Majklzbastlirny/WeatherStation/Code/Frontend/NodeRED/NodeRed-Flow.png

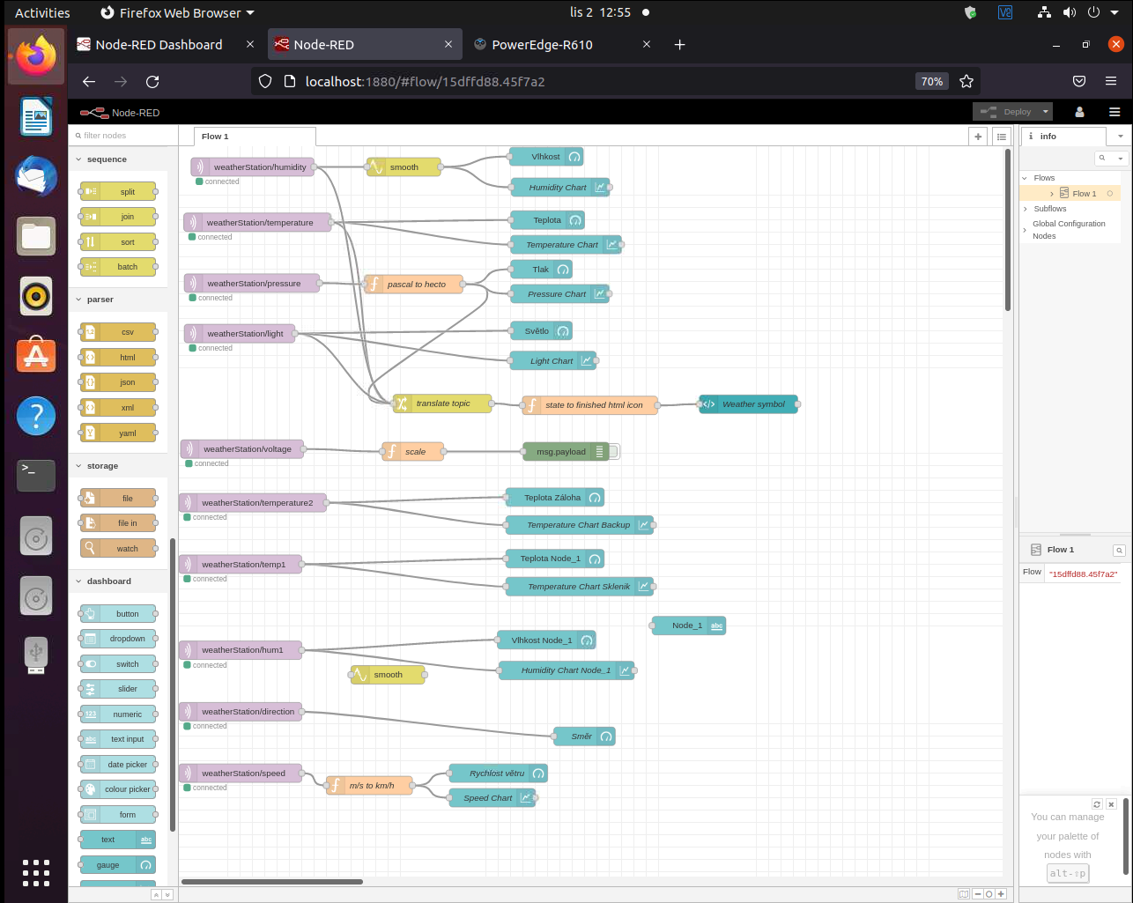
Code/Frontend/NodeRED/NodeRed-Flow.png
