Majklzbastlirny/WeatherStation/Code/Frontend/NodeRED/NodeRed-GUI.png

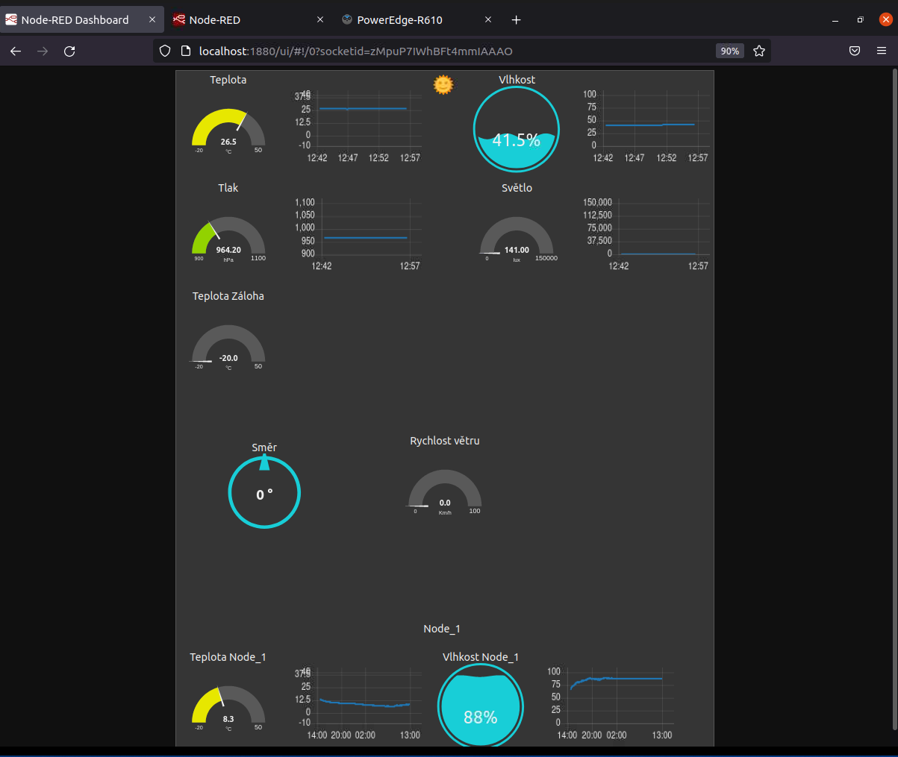
Code/Frontend/NodeRED/NodeRed-GUI.png
