Majklzbastlirny/WeatherStation/Documentation/1646741958582.jpg

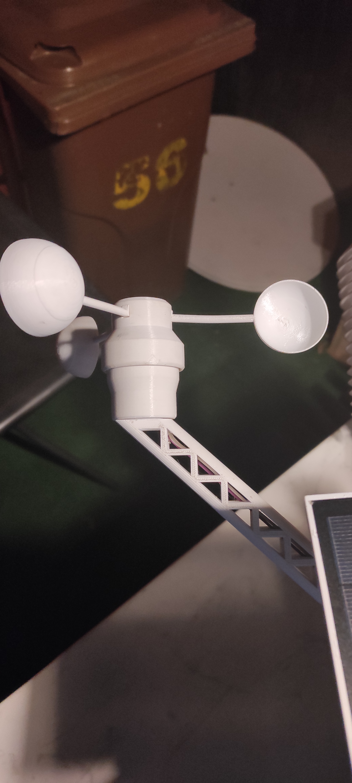
Documentation/1646741958582.jpg
