Majklzbastlirny/WeatherStation/Documentation/akumulátor.webp

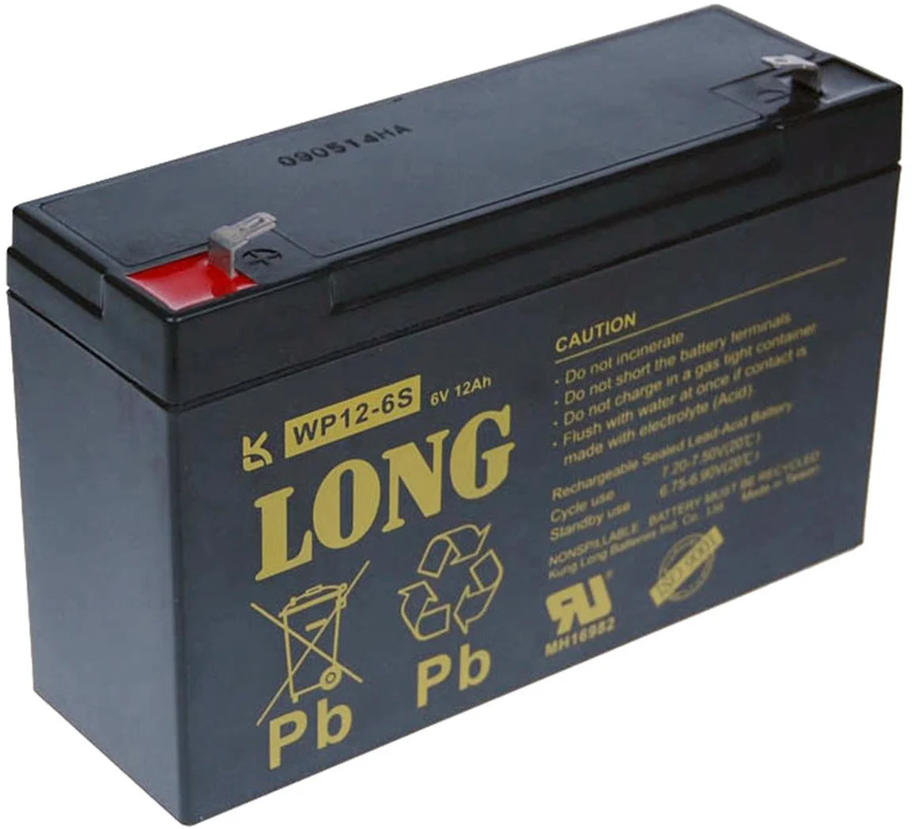
Documentation/akumulátor.webp
