Majklzbastlirny/WeatherStation/Documentation/Anemometr.jpg

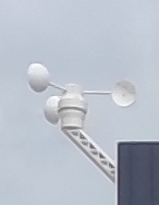
Documentation/Anemometr.jpg
