Majklzbastlirny/WeatherStation/Documentation/Anemometr_Base.png

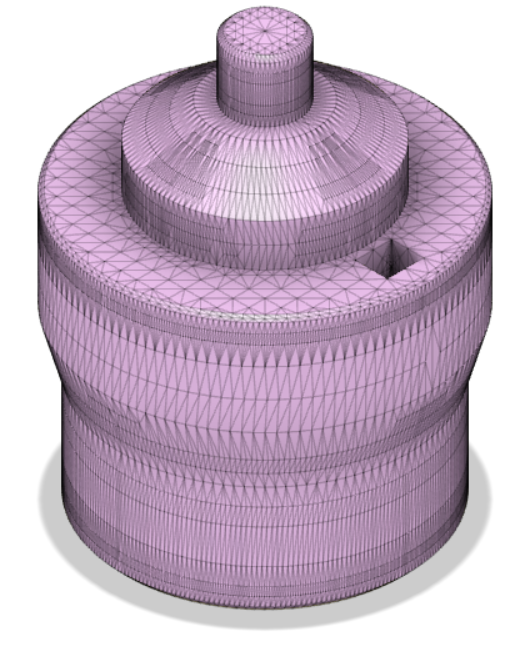
Documentation/Anemometr_Base.png
