Majklzbastlirny/WeatherStation/Documentation/Anemometr_Kryt.png

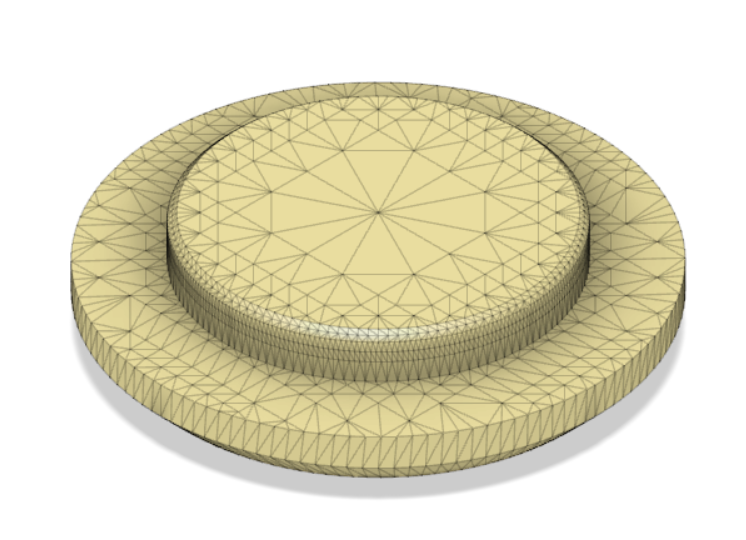
Documentation/Anemometr_Kryt.png
