Majklzbastlirny/WeatherStation/Documentation/Anemometr_Lopatka.png

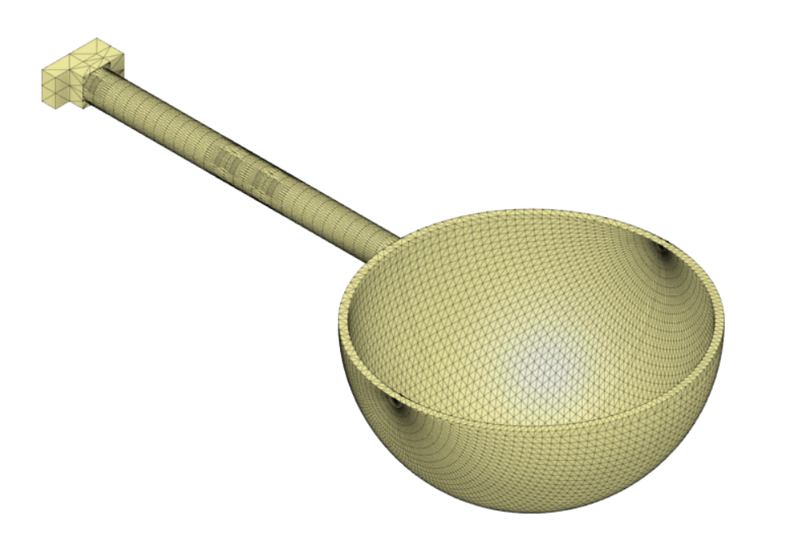
Documentation/Anemometr_Lopatka.png
