Majklzbastlirny/WeatherStation/Documentation/Anemometr_Tělo.png

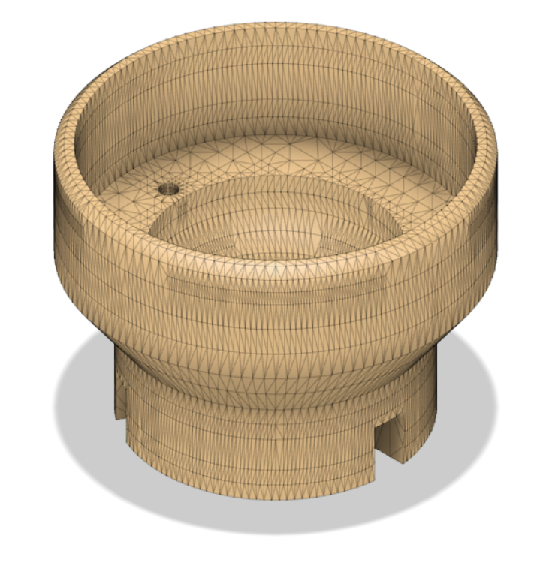
Documentation/Anemometr_Tělo.png
