Majklzbastlirny/WeatherStation/Documentation/BH1750.jpg

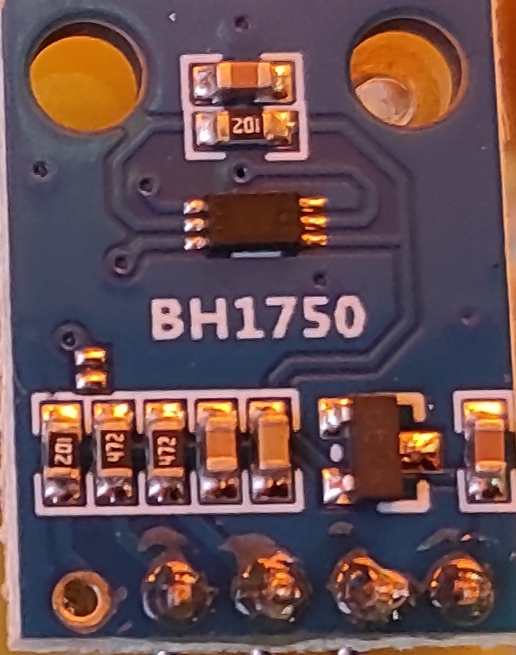
Documentation/BH1750.jpg
