Majklzbastlirny/WeatherStation/Documentation/blokove eink.png

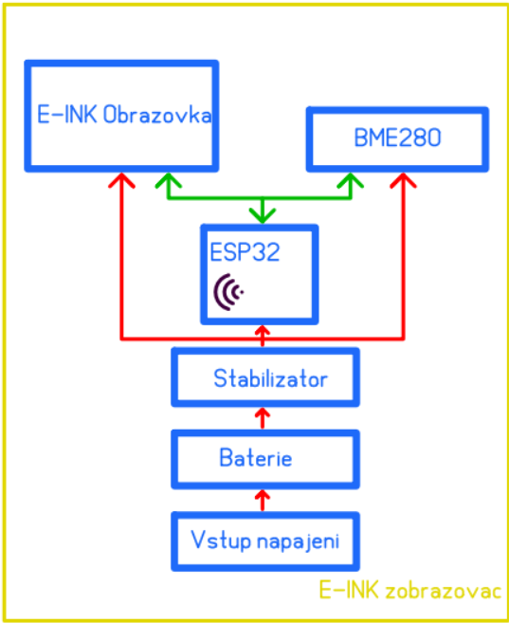
Documentation/blokove eink.png
