Majklzbastlirny/WeatherStation/Documentation/blokove meteo.png

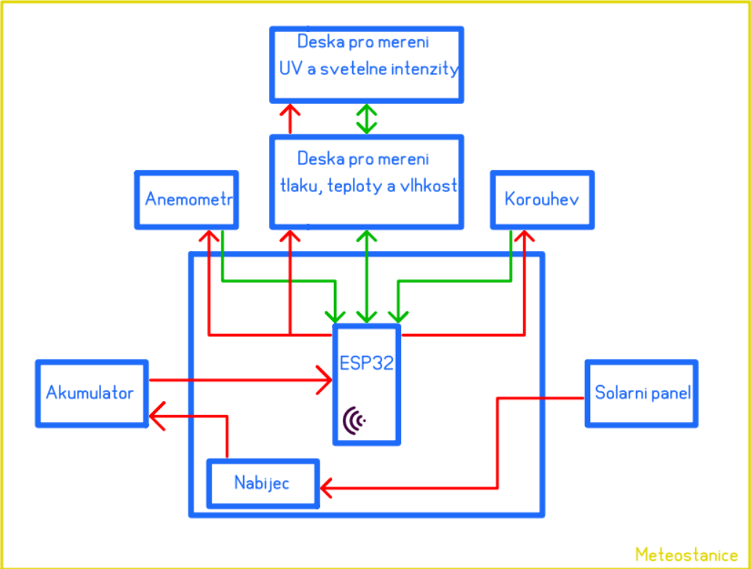
Documentation/blokove meteo.png
