Majklzbastlirny/WeatherStation/Documentation/Blokove oled.png

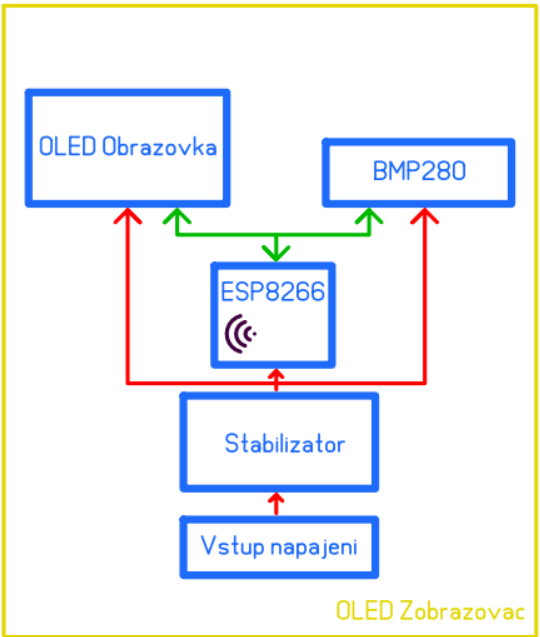
Documentation/Blokove oled.png
