Majklzbastlirny/WeatherStation/Documentation/BMP280.jpg

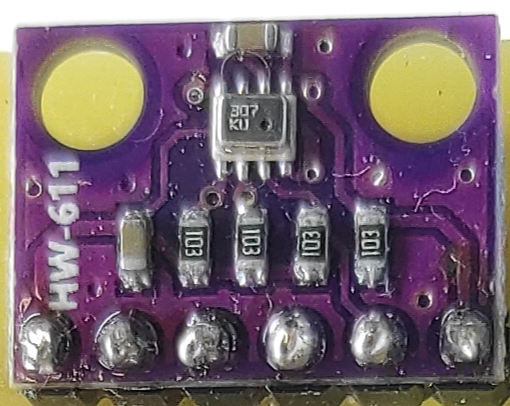
Documentation/BMP280.jpg
