Majklzbastlirny/WeatherStation/Documentation/Deska senzorů 1 - PCB/Deska senzorů 1 - PCB-1.png

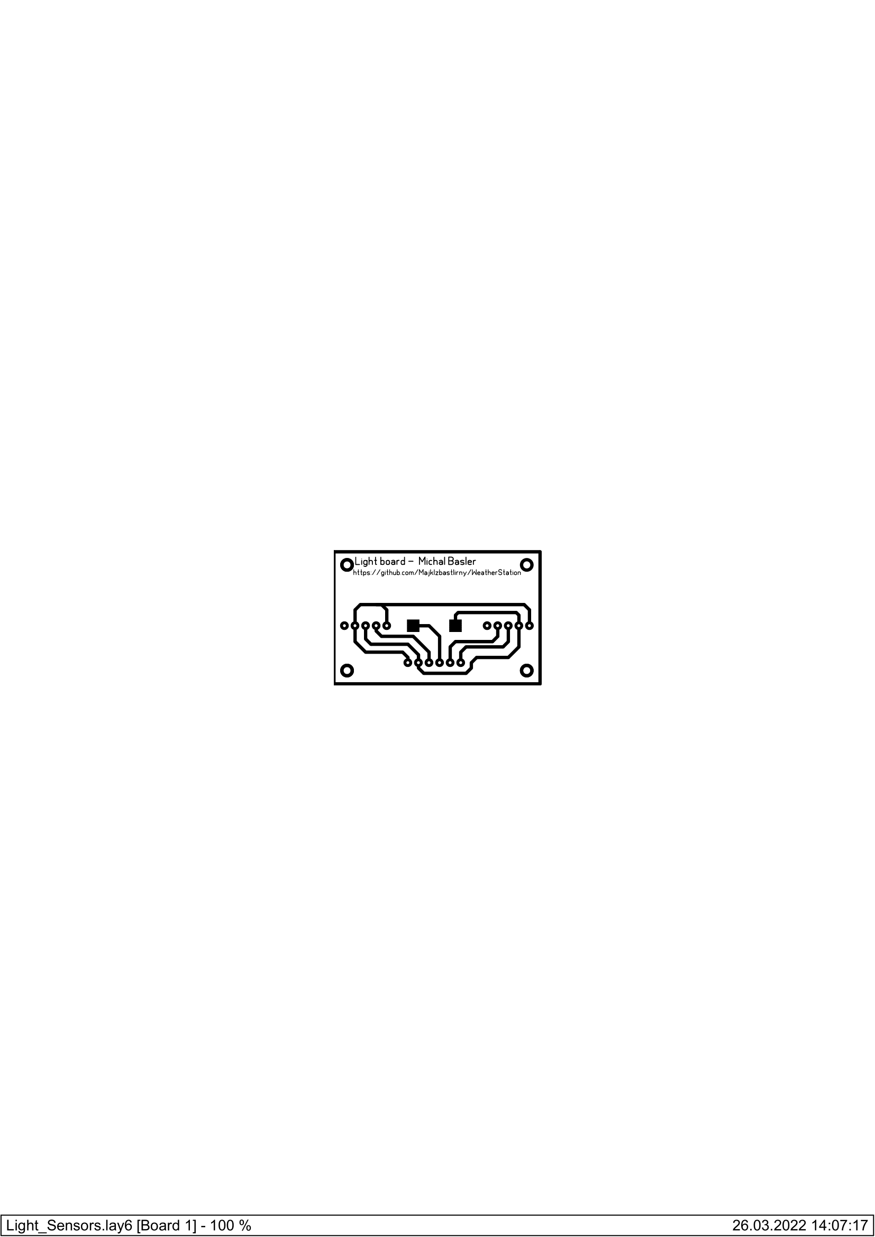
Documentation/Deska senzorů 1 - PCB/Deska senzorů 1 - PCB-1.png
