Majklzbastlirny/WeatherStation/Documentation/Deska senzorů 1/Deska senzorů 1-1.png

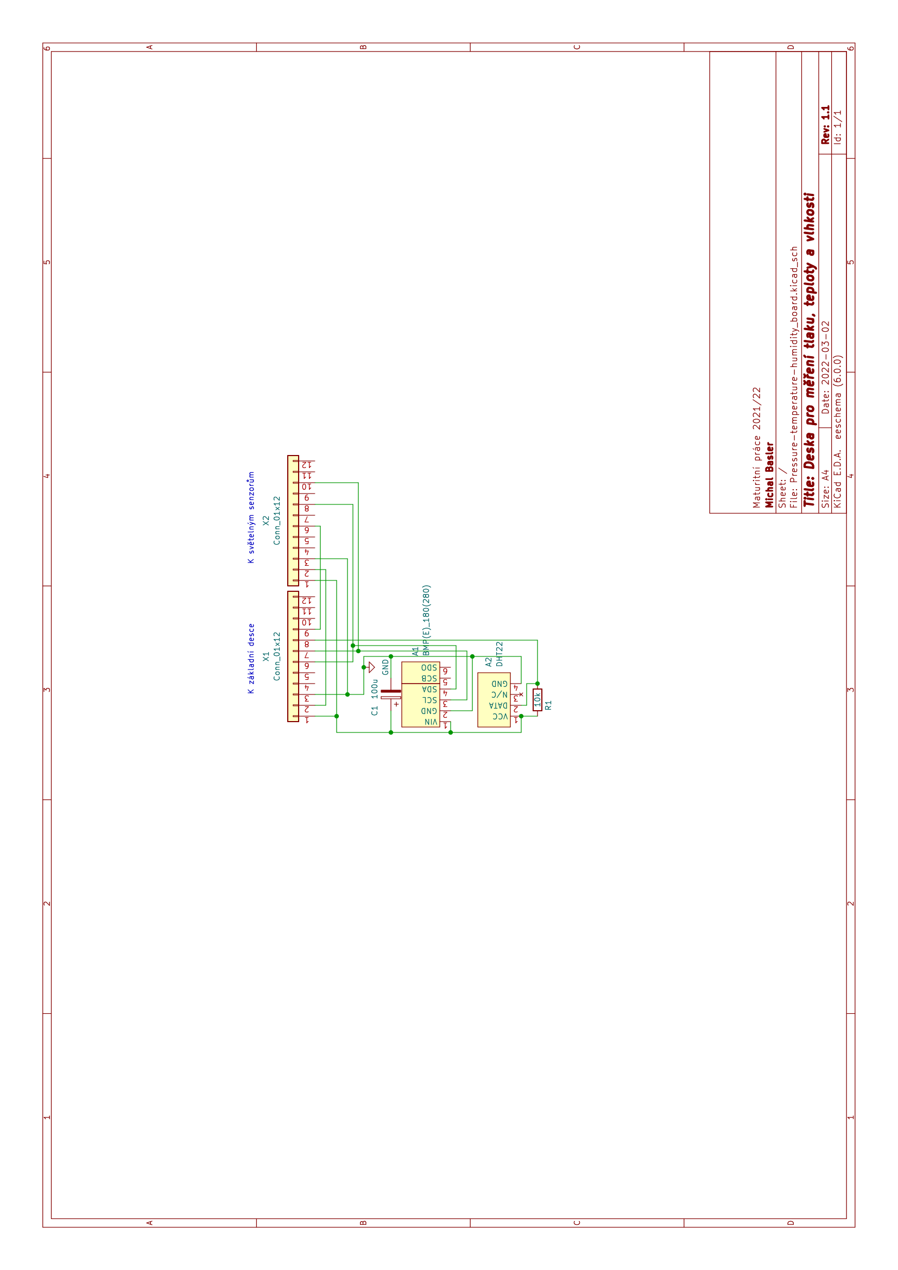
Documentation/Deska senzorů 1/Deska senzorů 1-1.png
