Majklzbastlirny/WeatherStation/Documentation/DHT22.jpg

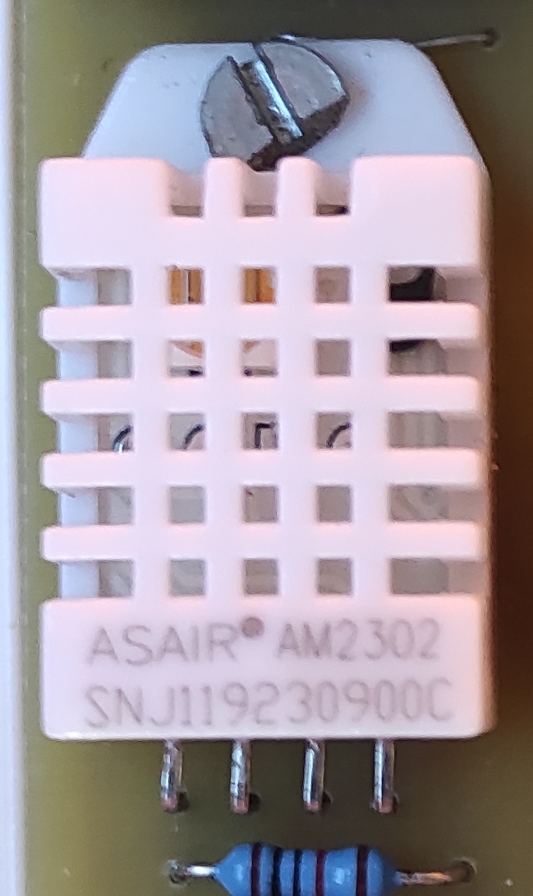
Documentation/DHT22.jpg
