Majklzbastlirny/WeatherStation/Documentation/Držák_Anemometr.png

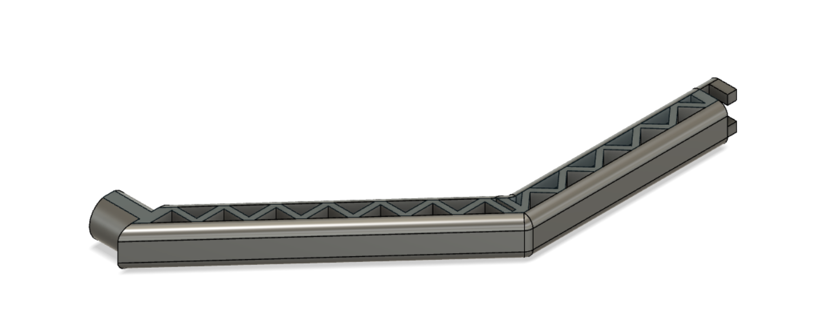
Documentation/Držák_Anemometr.png
