Majklzbastlirny/WeatherStation/Documentation/Držák_Korouhev.png

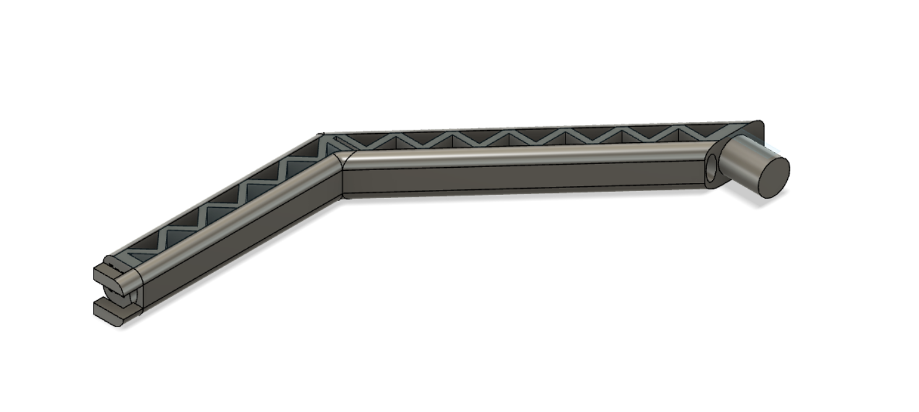
Documentation/Držák_Korouhev.png
