Majklzbastlirny/WeatherStation/Documentation/Držák_Senzory.png

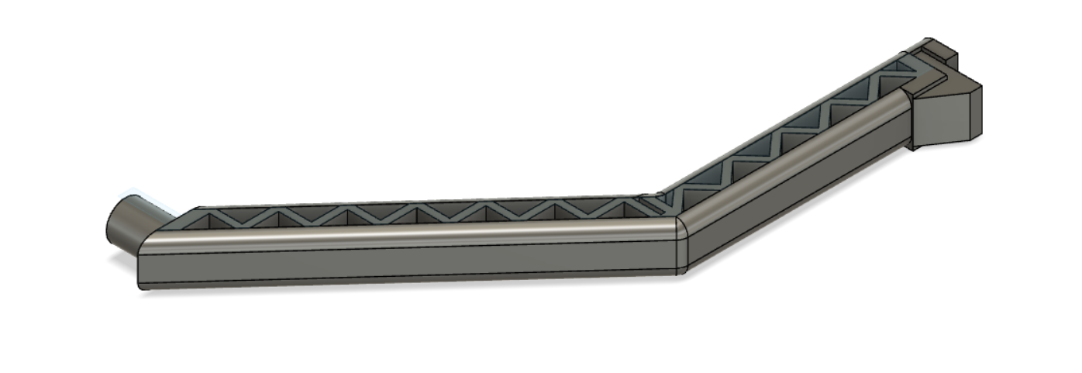
Documentation/Držák_Senzory.png
