Majklzbastlirny/WeatherStation/Documentation/Držák_Vše.png

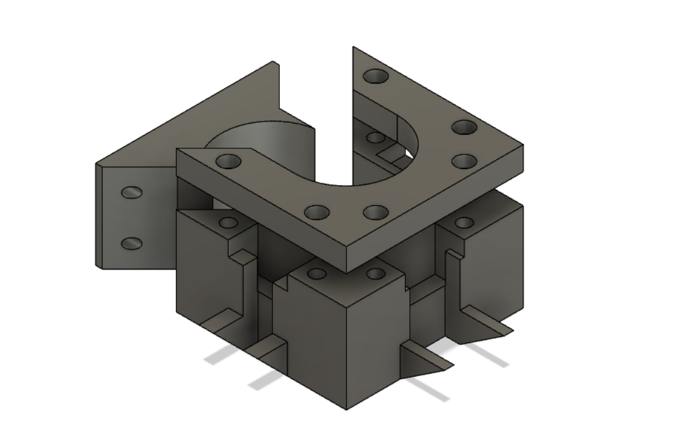
Documentation/Držák_Vše.png
