Majklzbastlirny/WeatherStation/Documentation/ESP_32.jpg

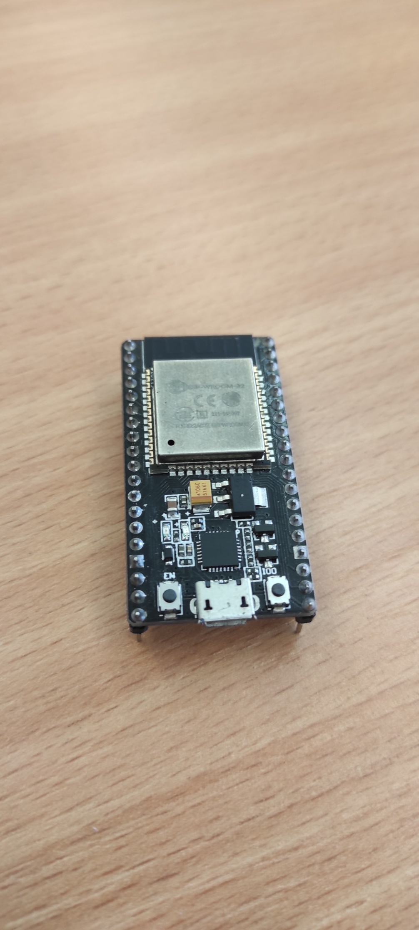
Documentation/ESP_32.jpg
