Majklzbastlirny/WeatherStation/Documentation/Home_Unit-OLED_Traces.BMP

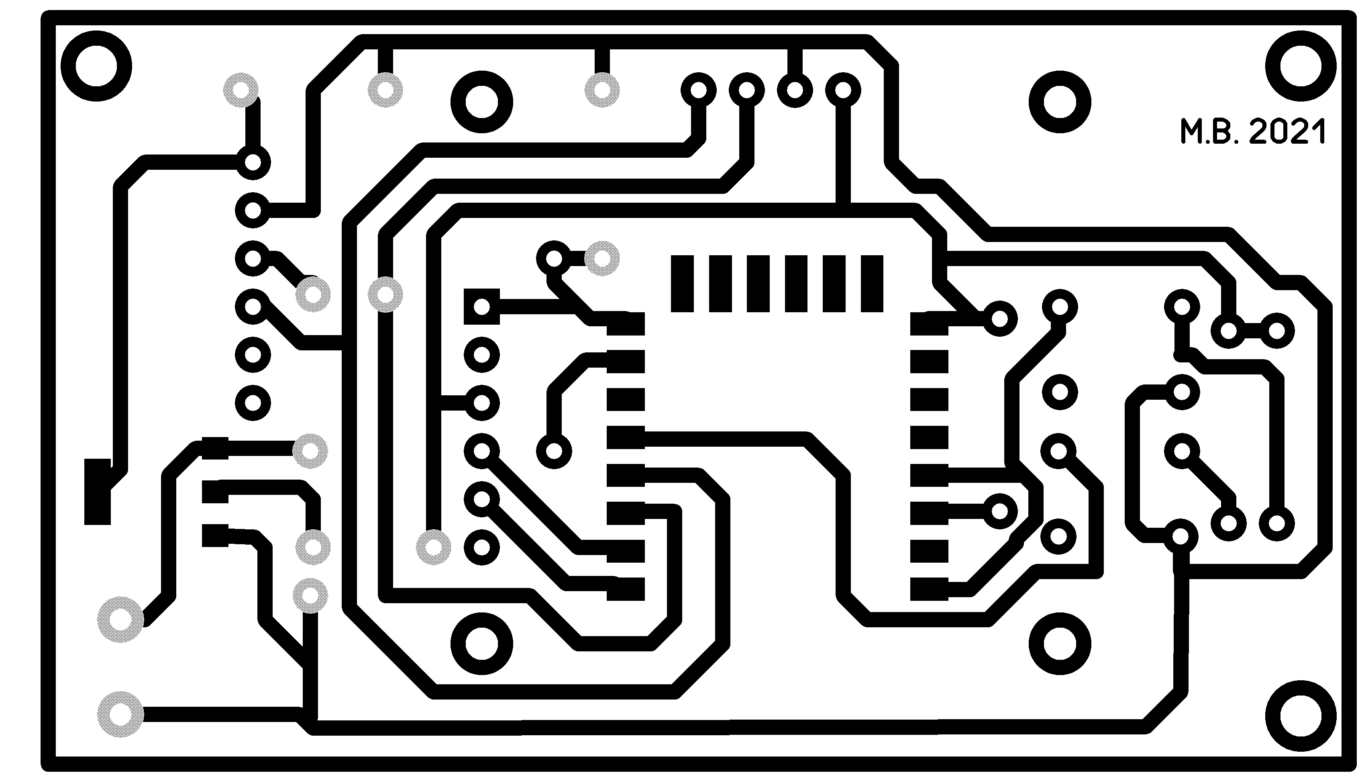
Documentation/Home_Unit-OLED_Traces.BMP
