Majklzbastlirny/WeatherStation/Documentation/IMG_20211102_125426.jpg

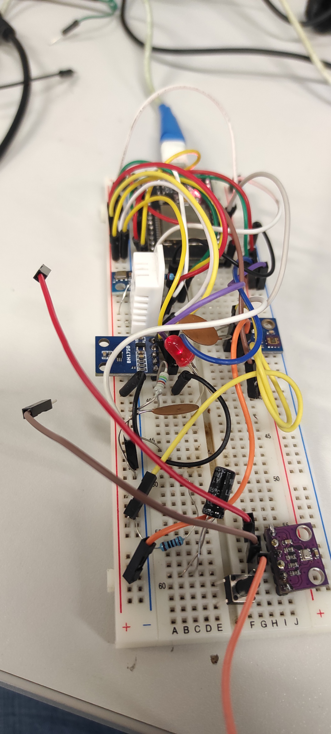
Documentation/IMG_20211102_125426.jpg
