Majklzbastlirny/WeatherStation/Documentation/IMG_20220214_152526.jpg

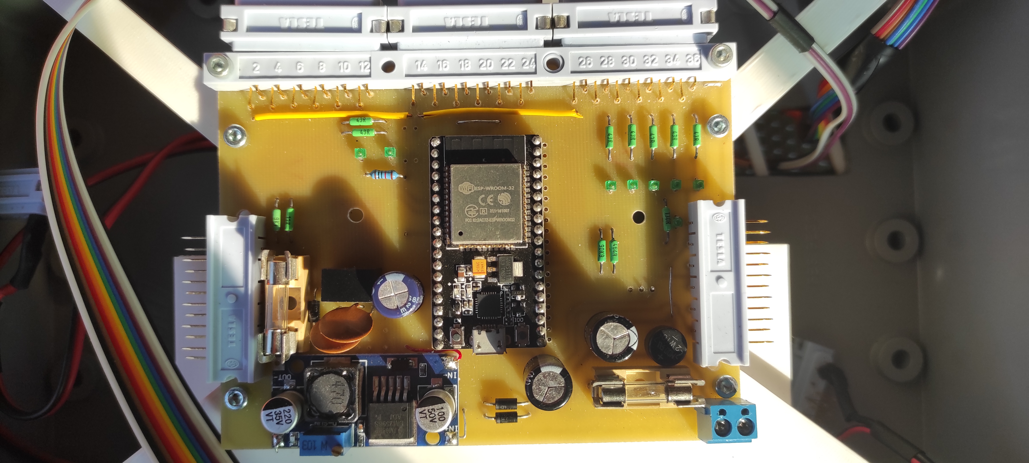
Documentation/IMG_20220214_152526.jpg
