Majklzbastlirny/WeatherStation/Documentation/IMG_20220214_152532.jpg

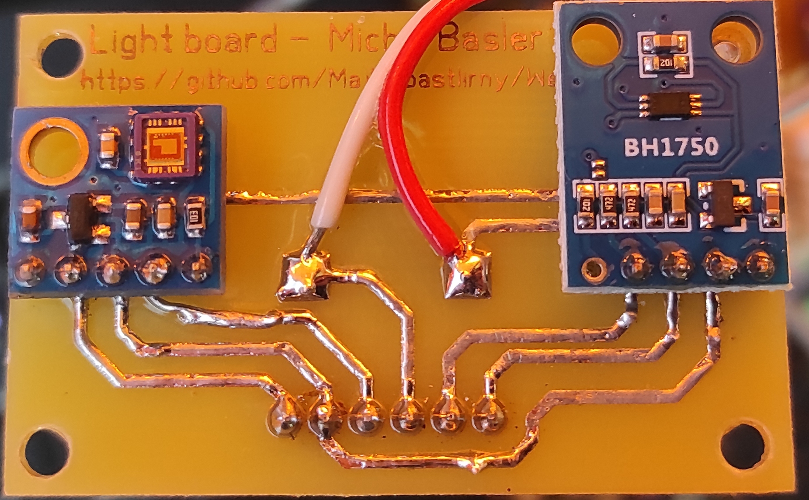
Documentation/IMG_20220214_152532.jpg
