Majklzbastlirny/WeatherStation/Documentation/IMG_20220214_152558.jpg

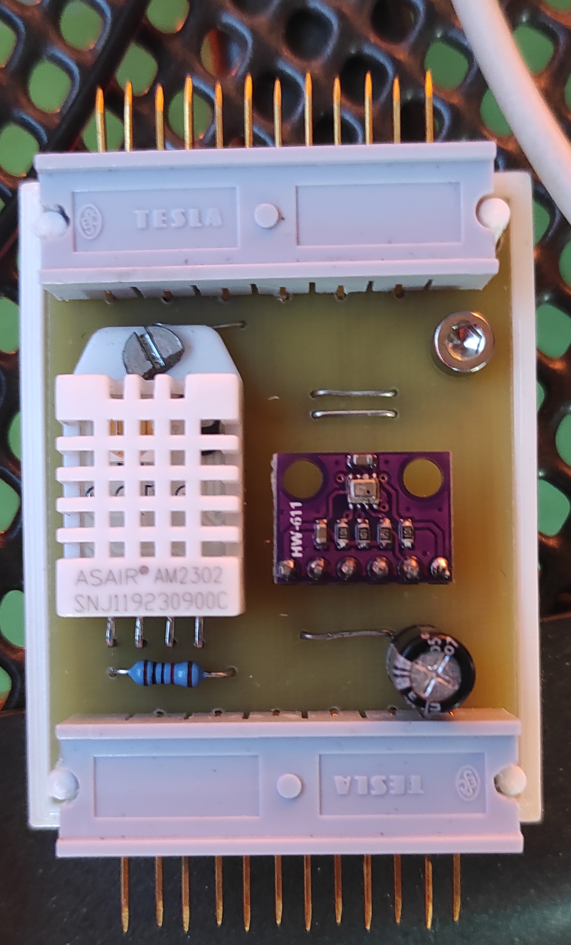
Documentation/IMG_20220214_152558.jpg
