Majklzbastlirny/WeatherStation/Documentation/IMG_20220214_160920.jpg

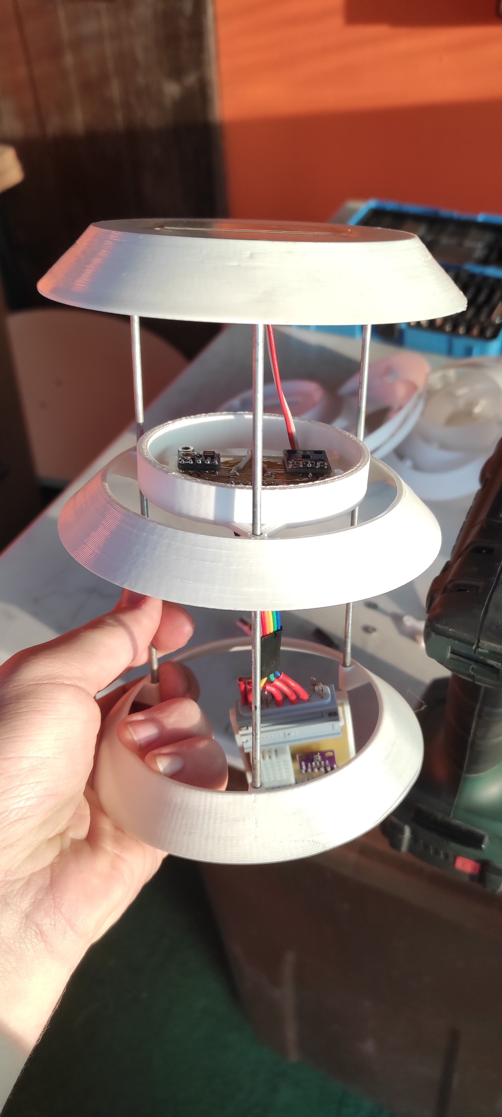
Documentation/IMG_20220214_160920.jpg
