Majklzbastlirny/WeatherStation/Documentation/IMG_20220302_161140.jpg

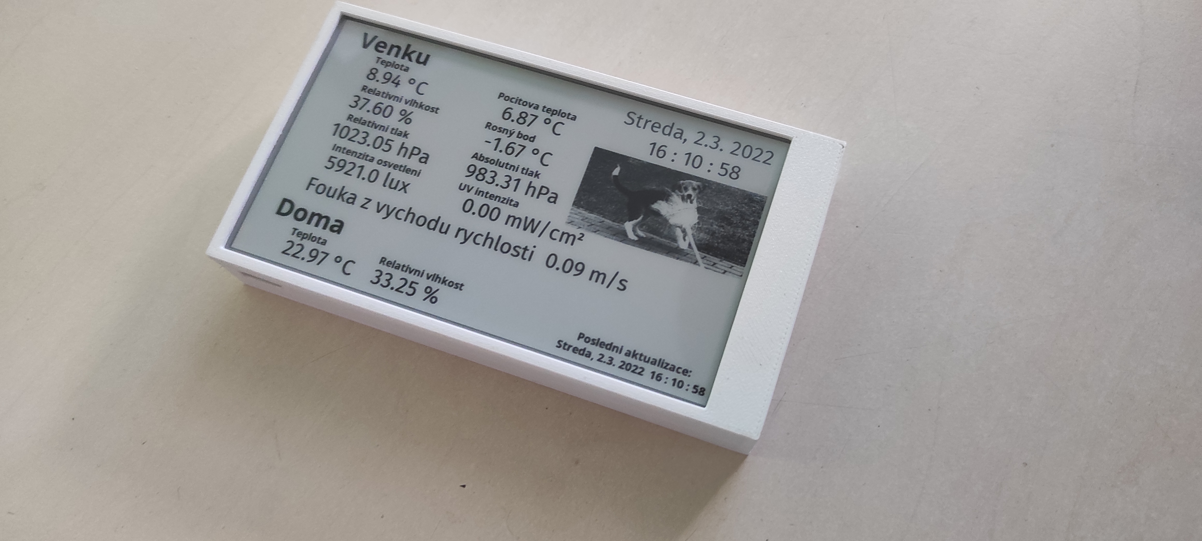
Documentation/IMG_20220302_161140.jpg
