Majklzbastlirny/WeatherStation/Documentation/IMG_20220302_161202.jpg

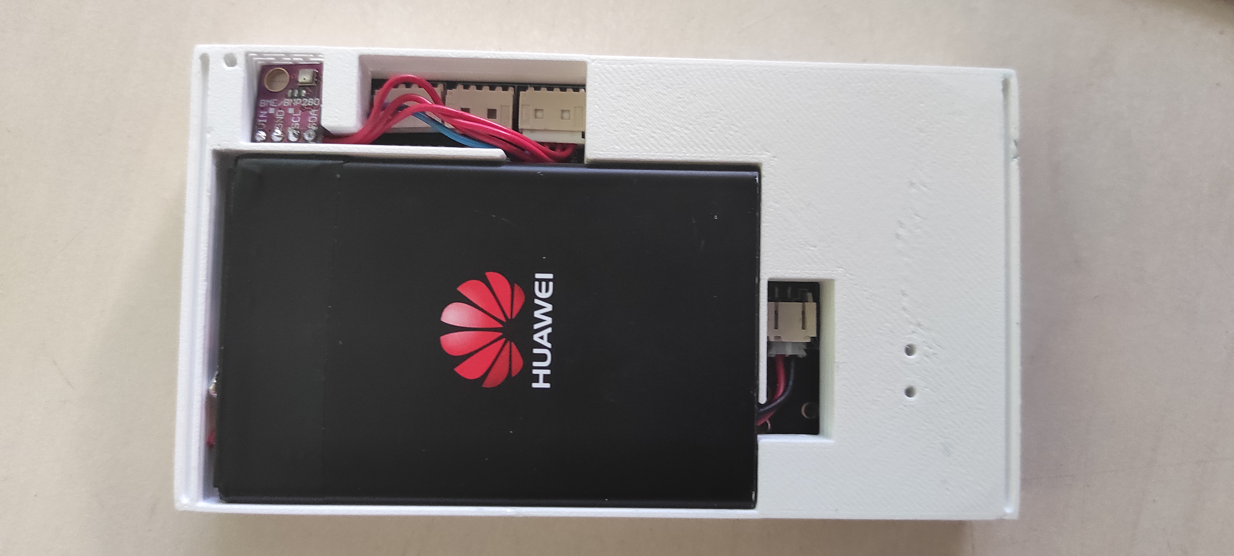
Documentation/IMG_20220302_161202.jpg
