Majklzbastlirny/WeatherStation/Documentation/IMG_20220303_124802.jpg

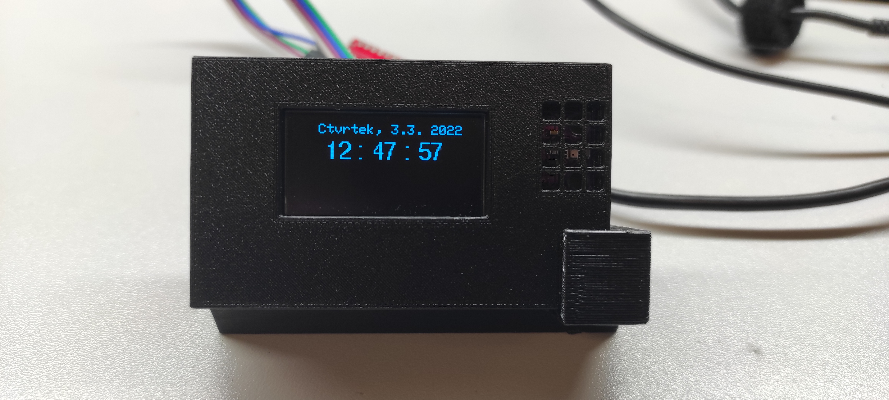
Documentation/IMG_20220303_124802.jpg
