Majklzbastlirny/WeatherStation/Documentation/IMG_20220303_124805.jpg

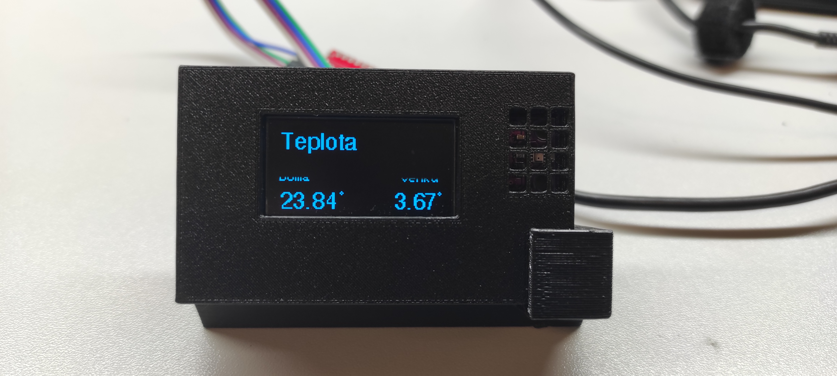
Documentation/IMG_20220303_124805.jpg
