Majklzbastlirny/WeatherStation/Documentation/IMG_20220303_124854.jpg

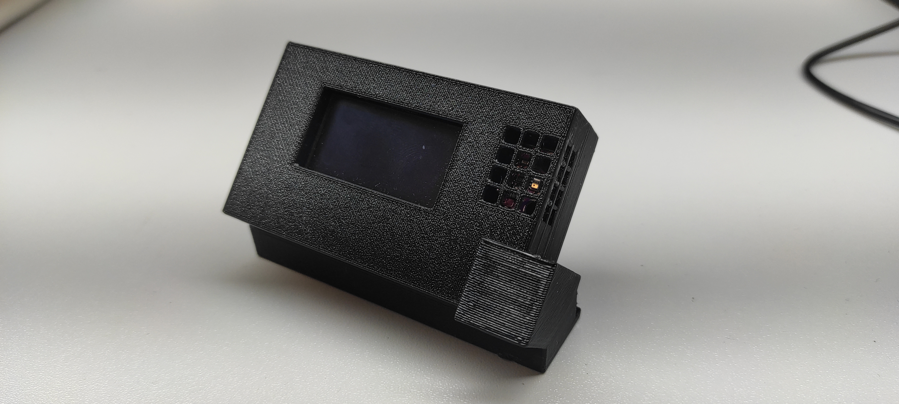
Documentation/IMG_20220303_124854.jpg
