Majklzbastlirny/WeatherStation/Documentation/IMG_20220303_124949.jpg

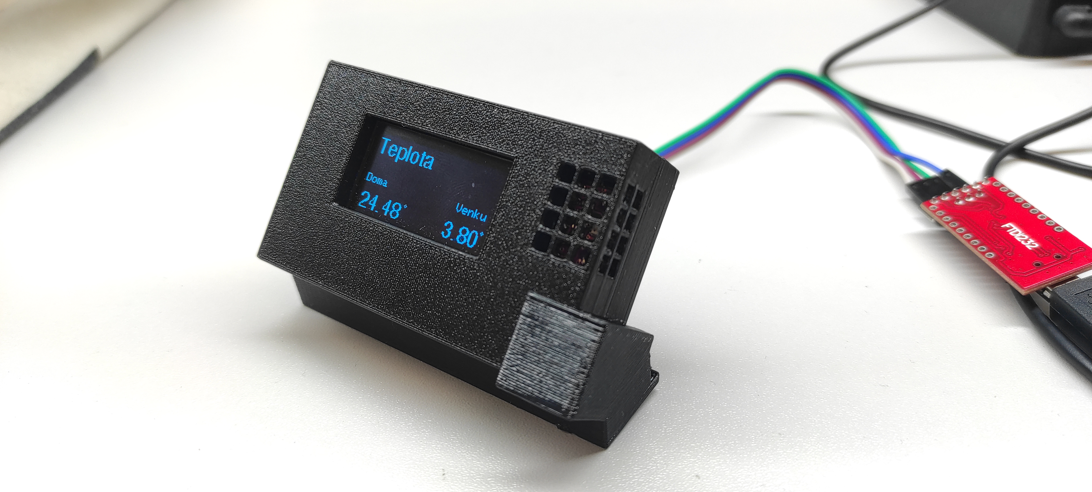
Documentation/IMG_20220303_124949.jpg
