Majklzbastlirny/WeatherStation/Documentation/IMG_20220303_125136_1.jpg

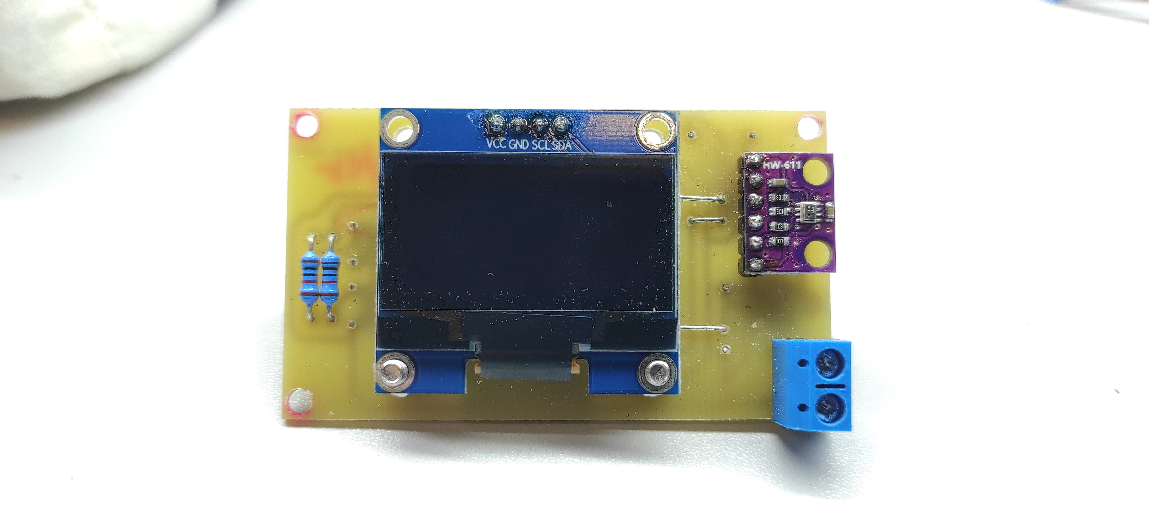
Documentation/IMG_20220303_125136_1.jpg
