Majklzbastlirny/WeatherStation/Documentation/IMG_20220303_125144.jpg

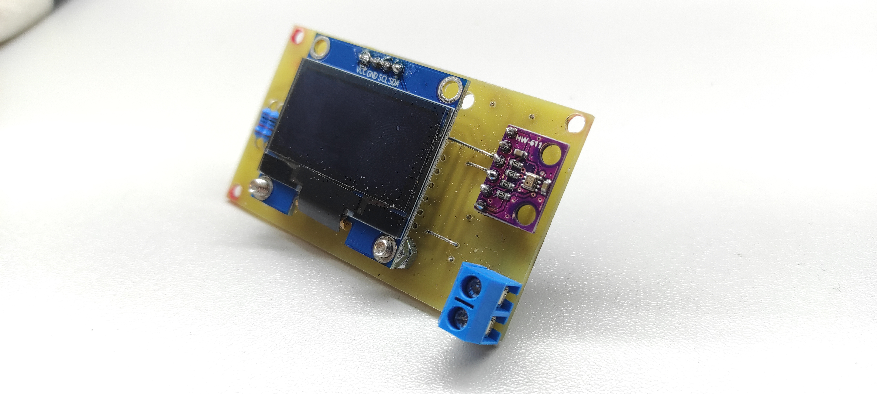
Documentation/IMG_20220303_125144.jpg
