Majklzbastlirny/WeatherStation/Documentation/Korouhev.jpg

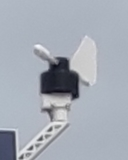
Documentation/Korouhev.jpg
