Majklzbastlirny/WeatherStation/Documentation/LED_Indikátory.jpg

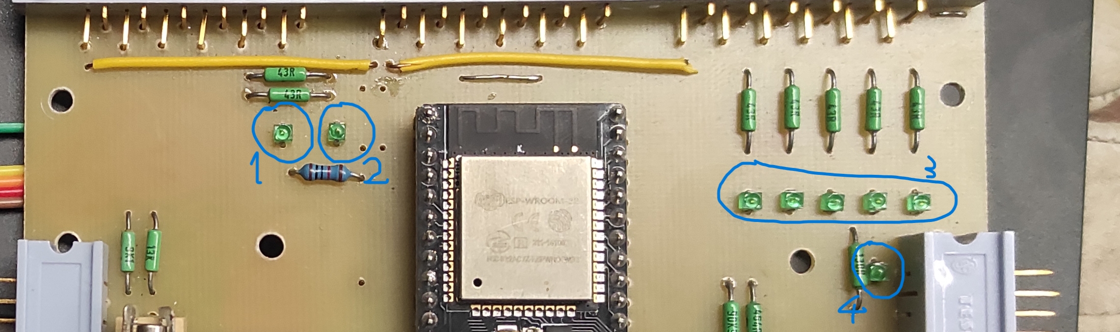
Documentation/LED_Indikátory.jpg
