Majklzbastlirny/WeatherStation/Documentation/Light_Board_Traces.BMP

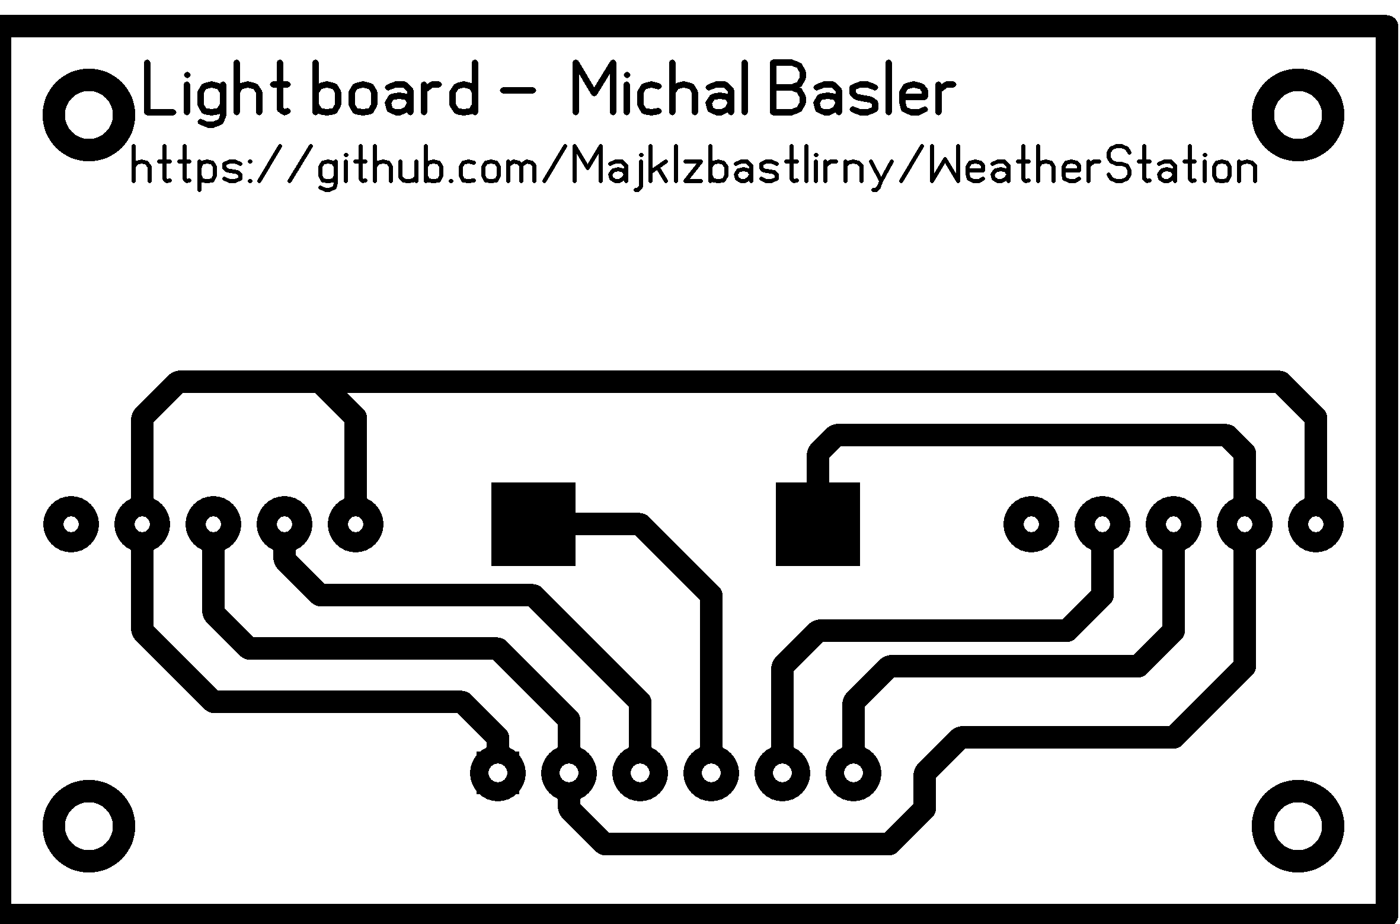
Documentation/Light_Board_Traces.BMP
