Majklzbastlirny/WeatherStation/Documentation/Main board - PCB/Main board - PCB-1.png

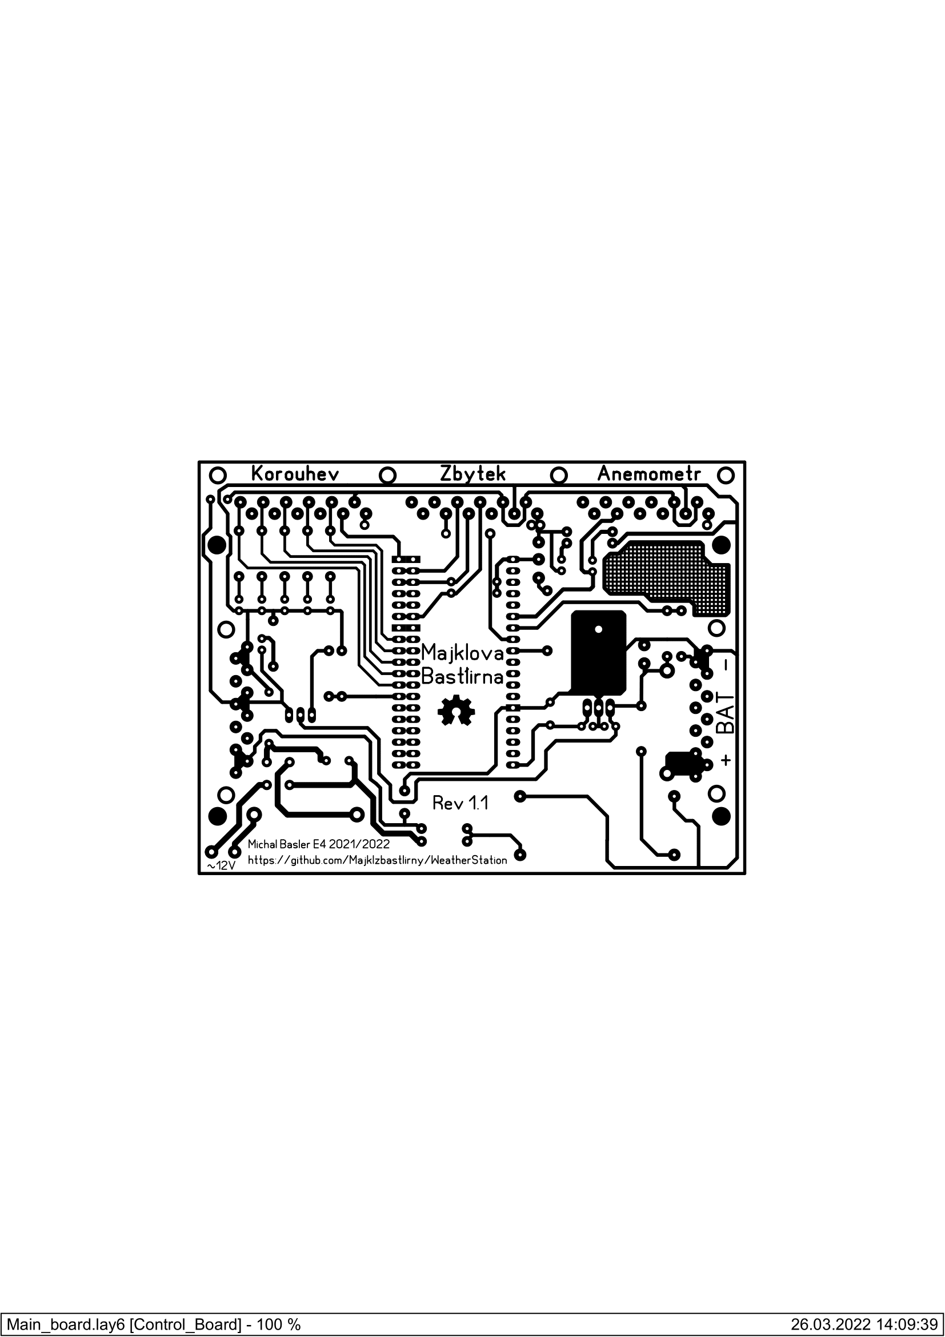
Documentation/Main board - PCB/Main board - PCB-1.png
