Majklzbastlirny/WeatherStation/Documentation/ML8511.jpg

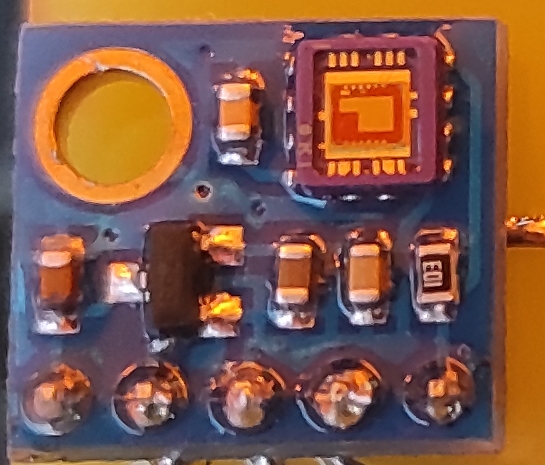
Documentation/ML8511.jpg
