Majklzbastlirny/WeatherStation/Documentation/Mounts.png

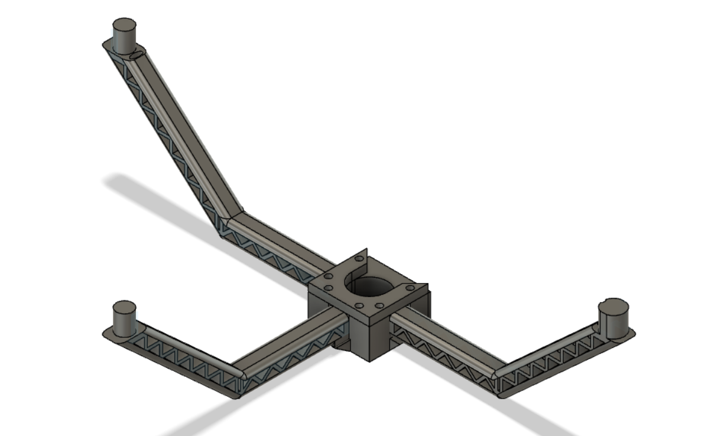
Documentation/Mounts.png
