Majklzbastlirny/WeatherStation/Documentation/OLED_Zobrazovač/OLED_Zobrazovač-1.png

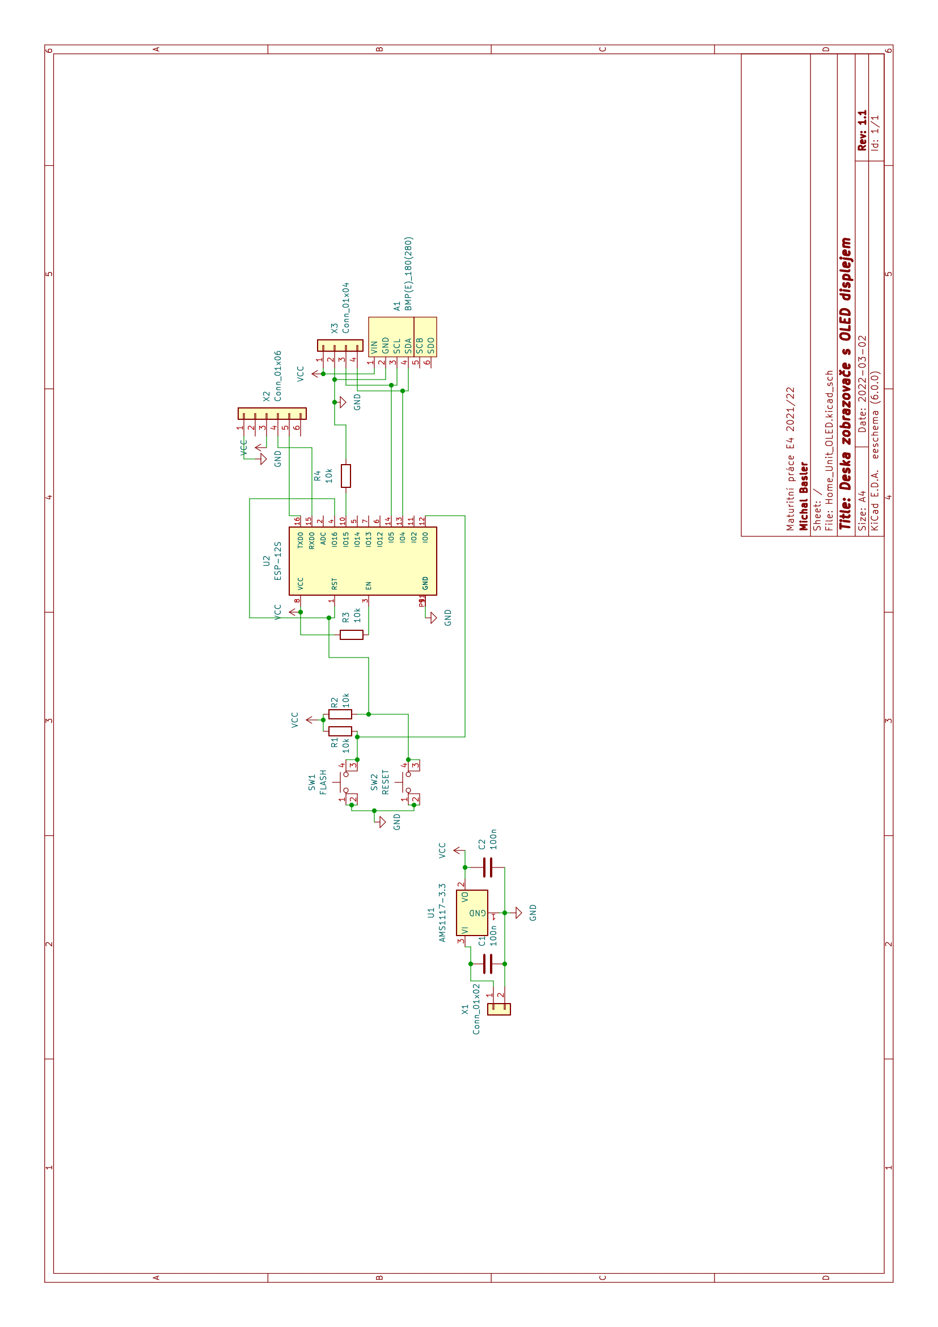
Documentation/OLED_Zobrazovač/OLED_Zobrazovač-1.png
