Majklzbastlirny/WeatherStation/Documentation/Osazovák_základnídeska.png

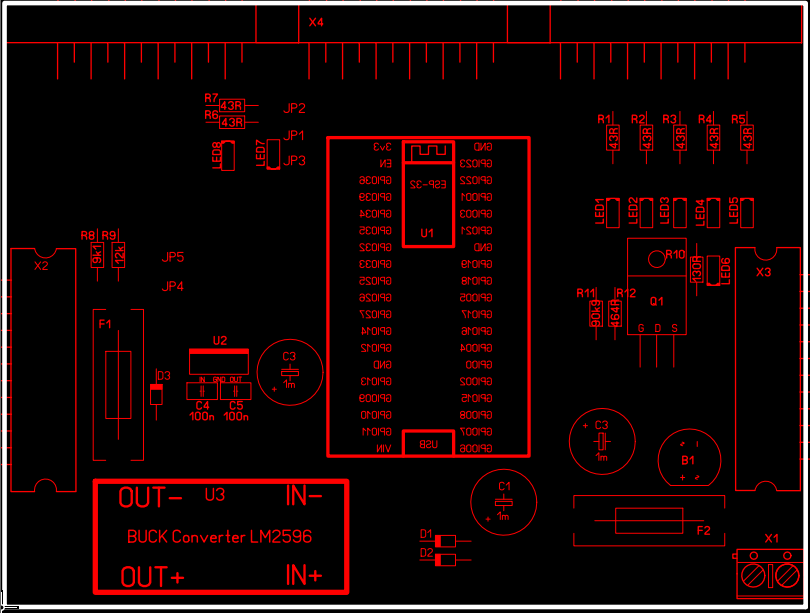
Documentation/Osazovák_základnídeska.png
