Majklzbastlirny/WeatherStation/Documentation/Screenshot_2022-04-21-14-04-22-356_com.mightyit.mqttclientterminal.jpg

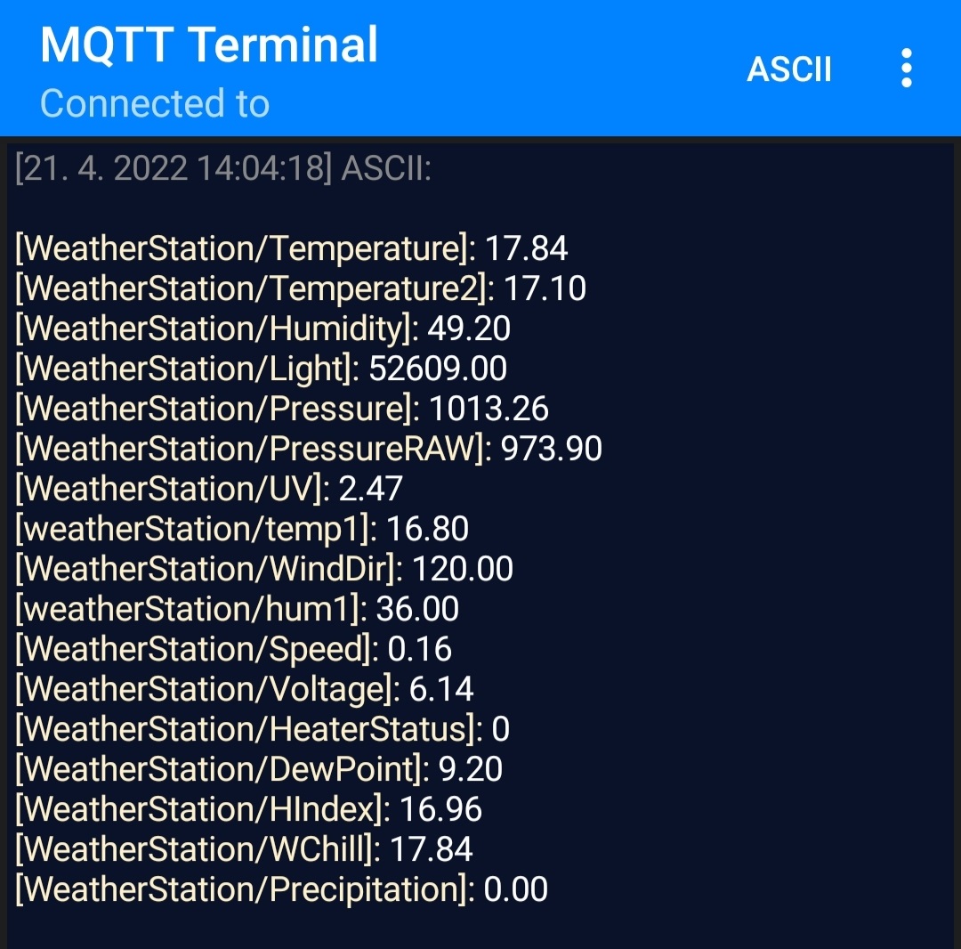
Documentation/Screenshot_2022-04-21-14-04-22-356_com.mightyit.mqttclientterminal.jpg
