Majklzbastlirny/WeatherStation/Documentation/Spínač-PCB/Spínač-PCB-1.png

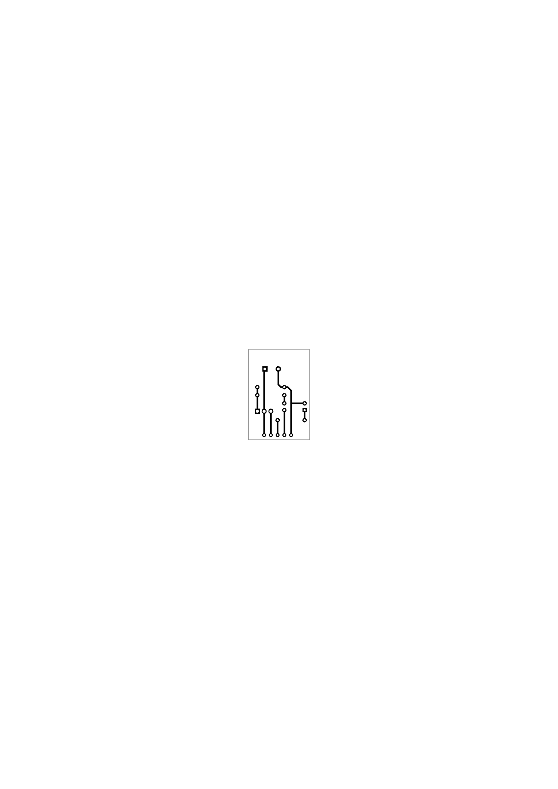
Documentation/Spínač-PCB/Spínač-PCB-1.png
