Majklzbastlirny/WeatherStation/Documentation/Switching_Obvody.jpg

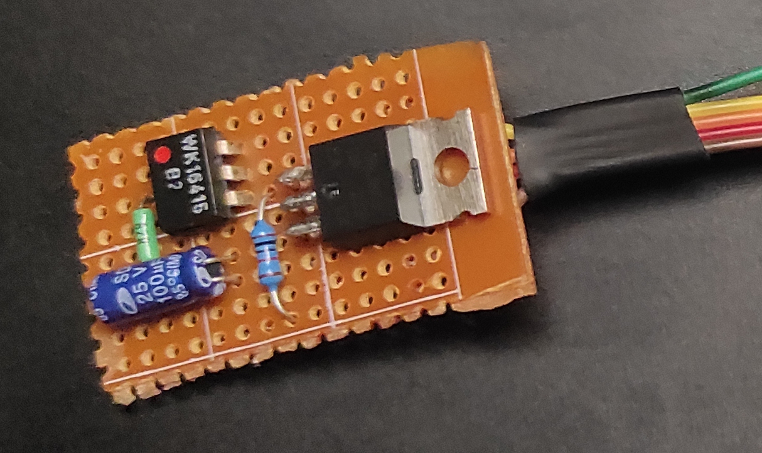
Documentation/Switching_Obvody.jpg
