Majklzbastlirny/WeatherStation/Documentation/Výsledek EINK.jpg

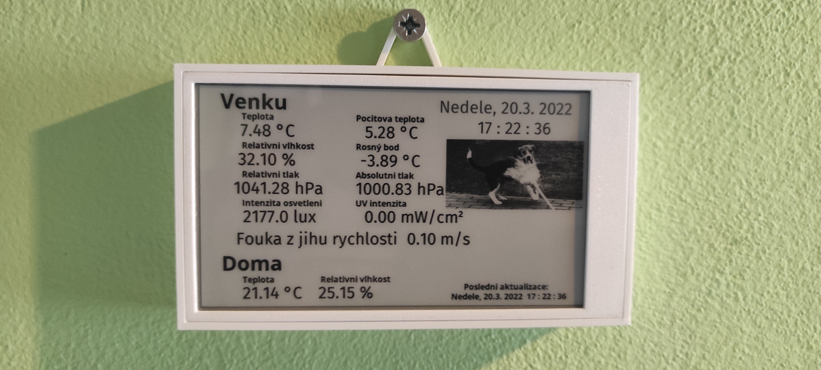
Documentation/Výsledek EINK.jpg
