Majklzbastlirny/WeatherStation/Documentation/Výsledek MQTT.jpg

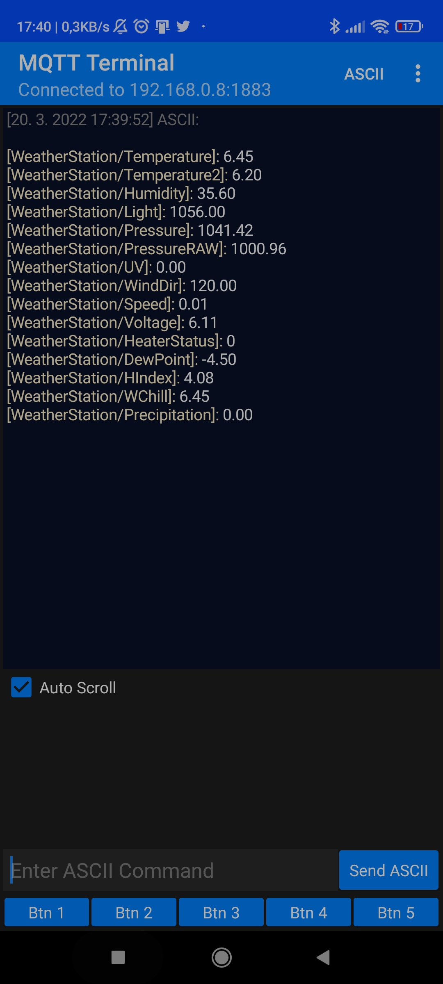
Documentation/Výsledek MQTT.jpg
