Majklzbastlirny/WeatherStation/Documentation/Výsledek OLED.jpg

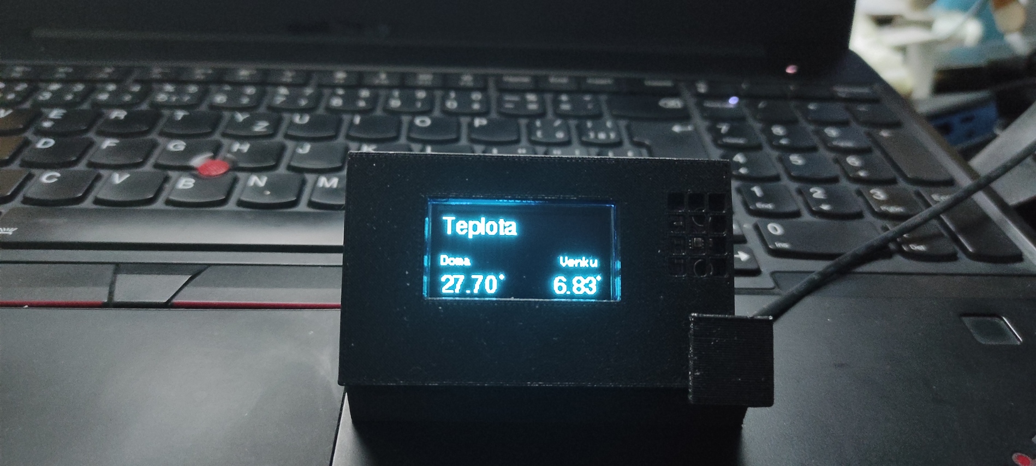
Documentation/Výsledek OLED.jpg
