Majklzbastlirny/WeatherStation/Documentation/Základka/Základní deska.png

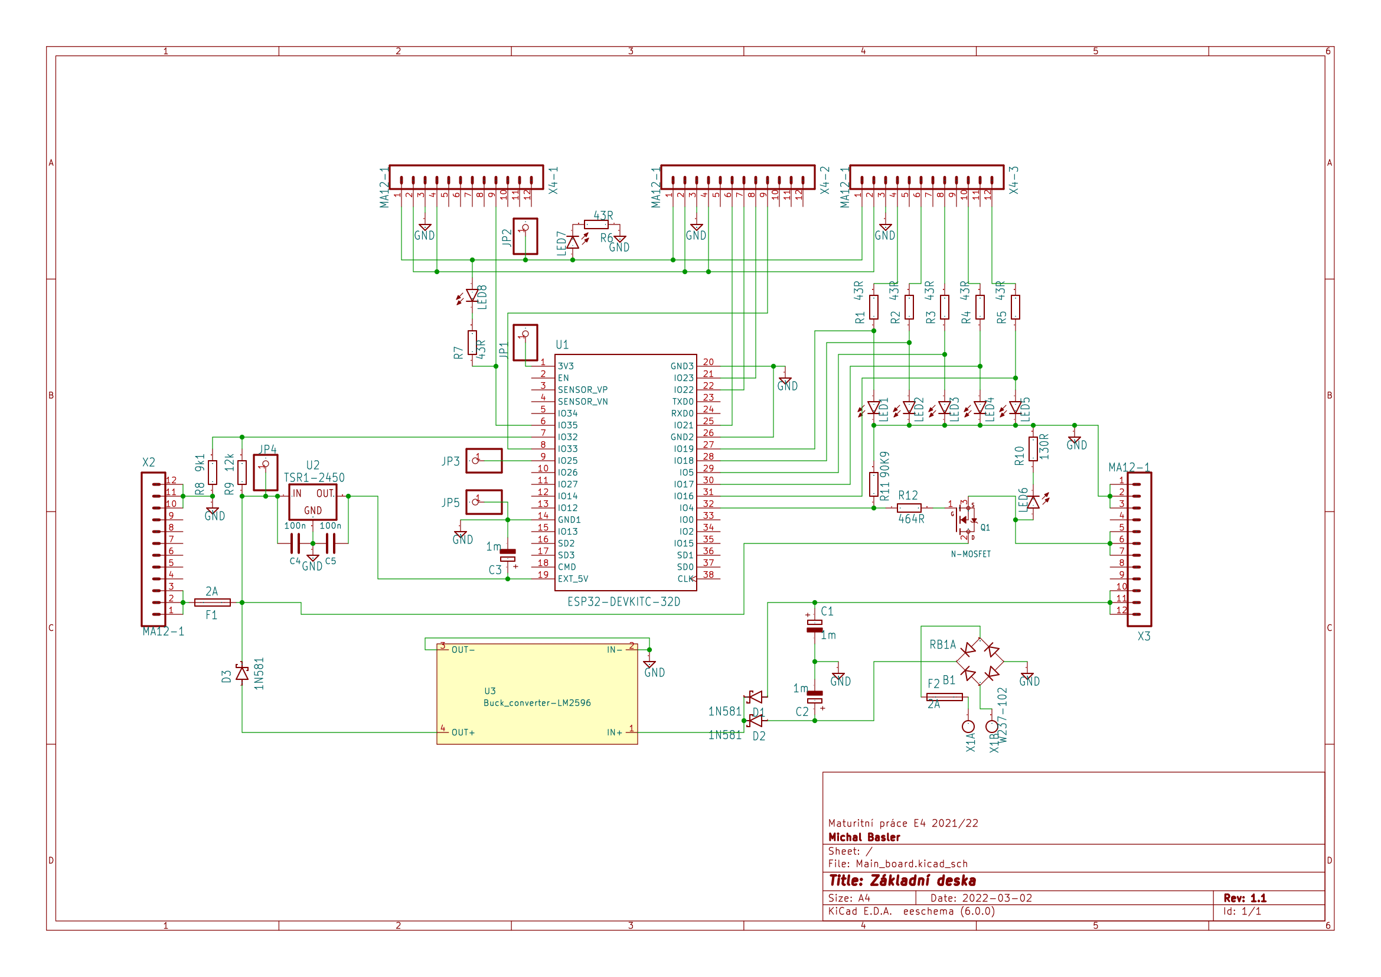
Documentation/Základka/Základní deska.png
