Majklzbastlirny/WeatherStation/Documentation/Štít-Držák.png

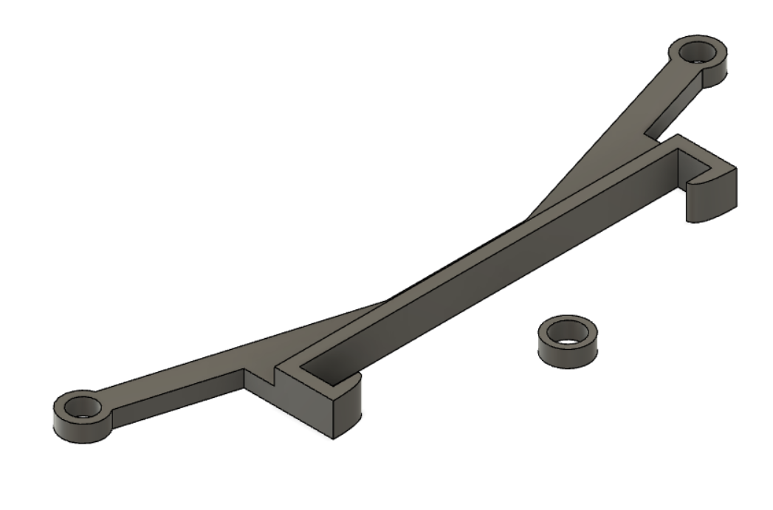
Documentation/Štít-Držák.png
