Majklzbastlirny/WeatherStation/Documentation/Štít-Kryt.png

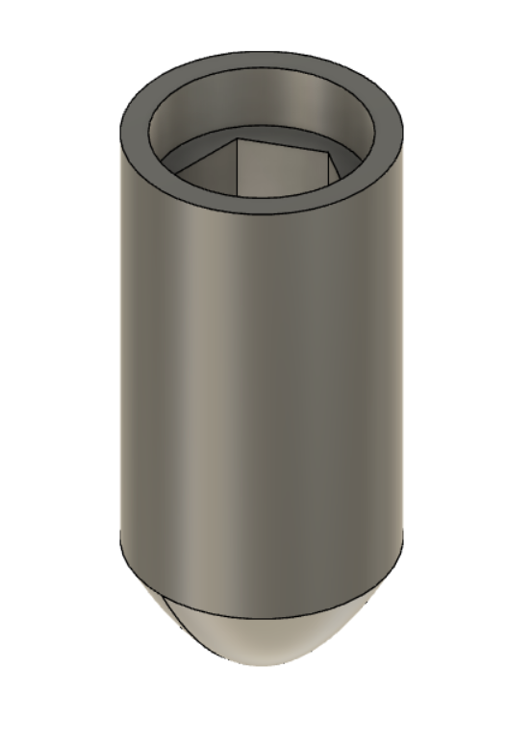
Documentation/Štít-Kryt.png
