Majklzbastlirny/WeatherStation/Documentation/Štít-Senzory.png

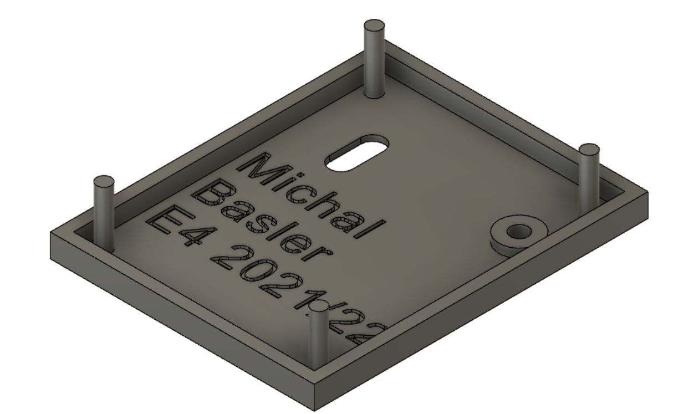
Documentation/Štít-Senzory.png
