Majklzbastlirny/WeatherStation/Documentation/Štít-Spodek.png

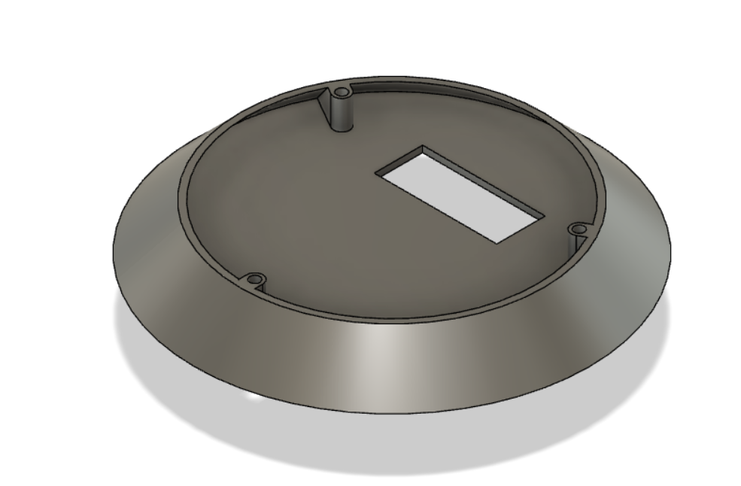
Documentation/Štít-Spodek.png
