Majklzbastlirny/WeatherStation/Documentation/Štít-Střed.png

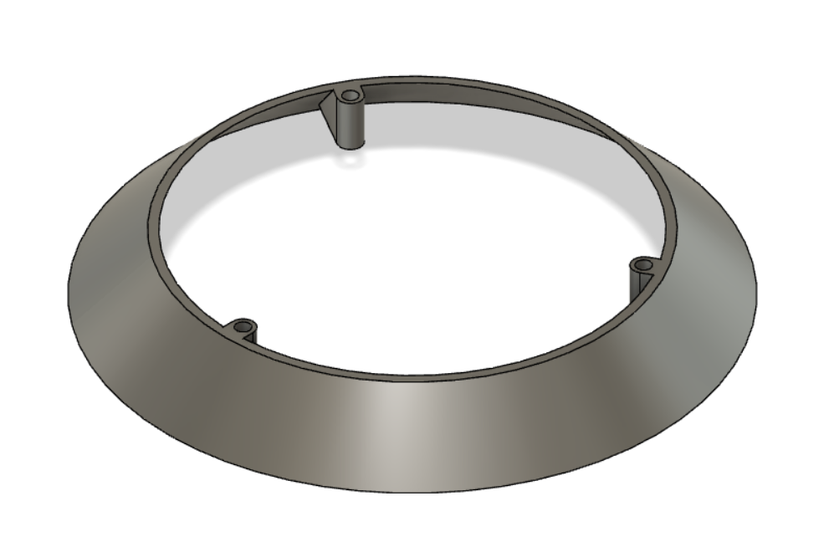
Documentation/Štít-Střed.png
