Majklzbastlirny/WeatherStation/Documentation/Štít-Světlo.png

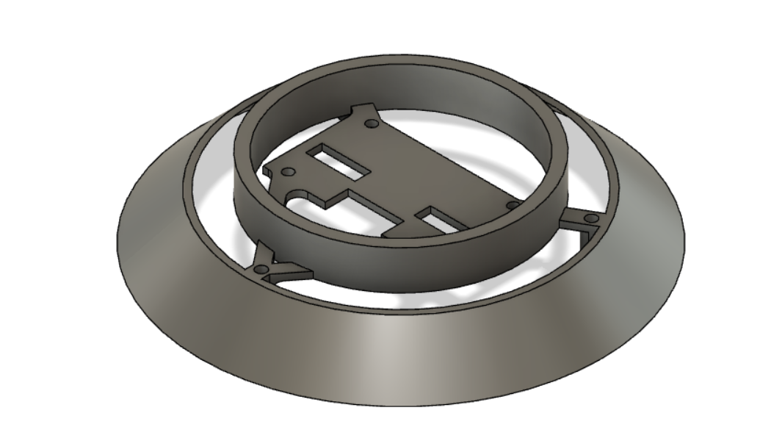
Documentation/Štít-Světlo.png
