Majklzbastlirny/WeatherStation/Documentation/Štít-Vrch-Bottom.png

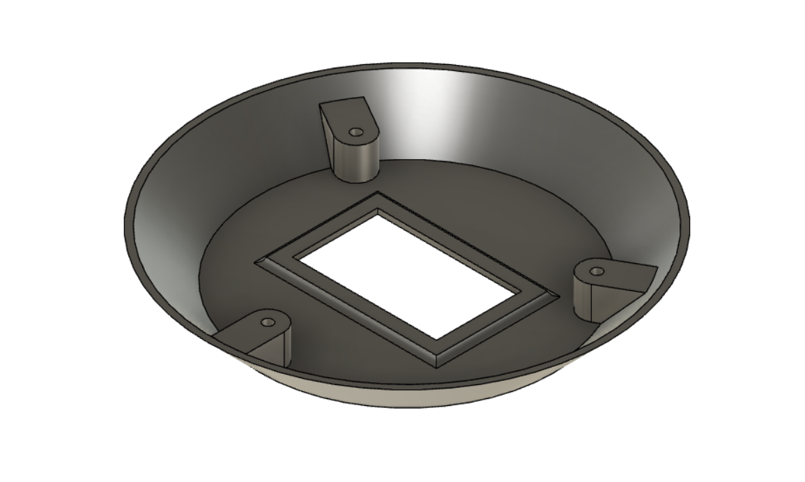
Documentation/Štít-Vrch-Bottom.png
