Majklzbastlirny/WeatherStation/Documentation/Štít-Vrch.png

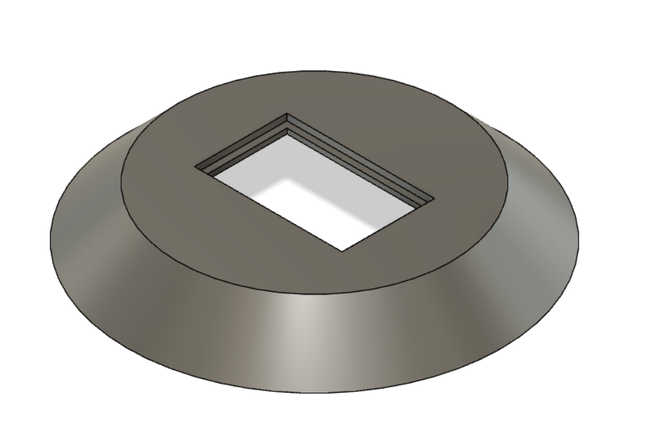
Documentation/Štít-Vrch.png
