Majklzbastlirny/WeatherStation/Hardware/PCBs and other pcb stuff/IMG_20211216_145908.jpg

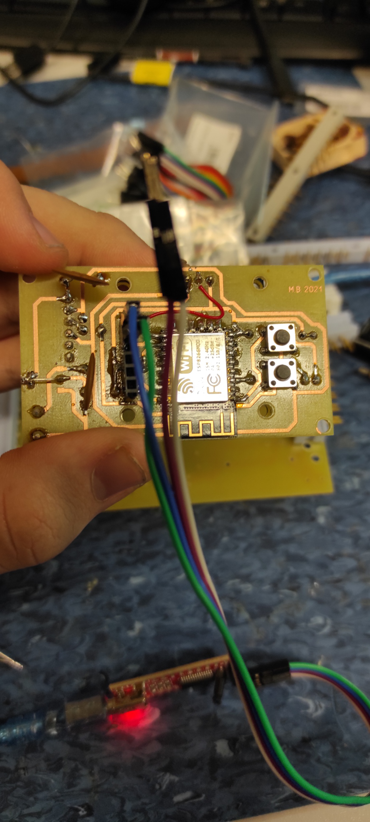
Hardware/PCBs and other pcb stuff/IMG_20211216_145908.jpg
