Majklzbastlirny/WeatherStation/Hardware/PCBs and other pcb stuff/IMG_20220117_113753.jpg

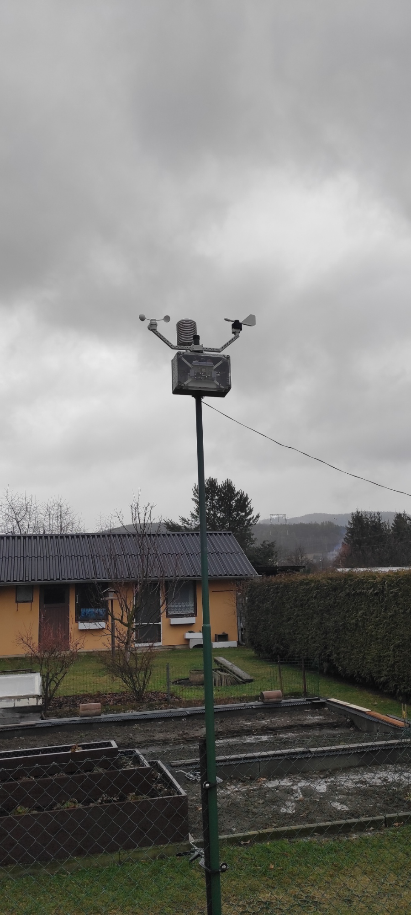
Hardware/PCBs and other pcb stuff/IMG_20220117_113753.jpg
