Majklzbastlirny/WeatherStation/Hardware/PCBs and other pcb stuff/IMG_20220117_113806.jpg

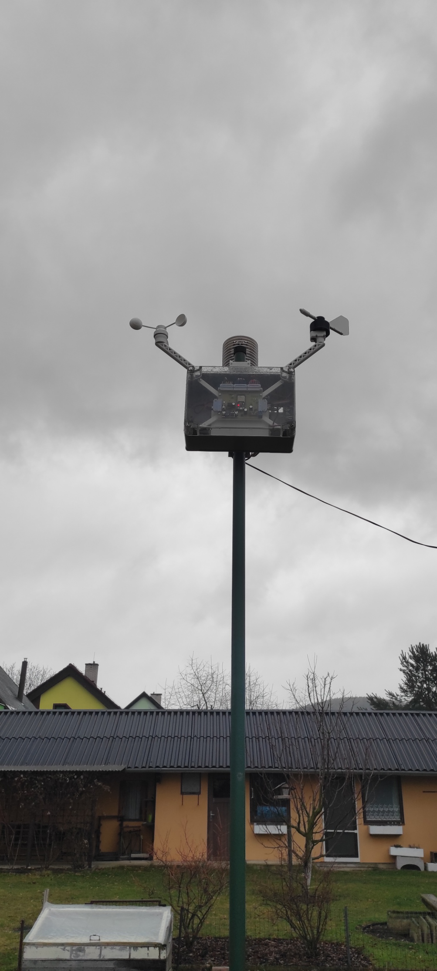
Hardware/PCBs and other pcb stuff/IMG_20220117_113806.jpg
