Majklzbastlirny/WeatherStation/Hardware/PCBs and other pcb stuff/Top_18.11.21.png

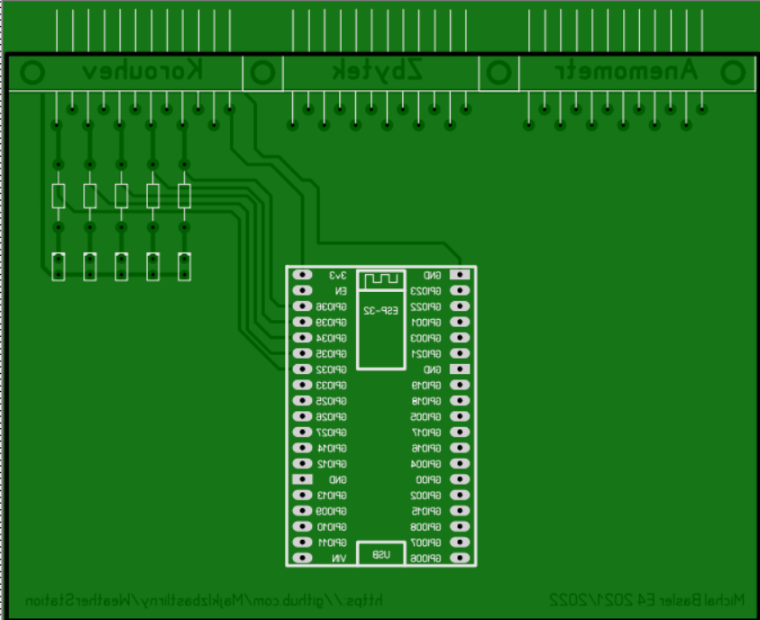
Hardware/PCBs and other pcb stuff/Top_18.11.21.png
