Majklzbastlirny/WeatherStation/Hardware/3D files/Solární panely/Solární panel - Klip 1.3mf

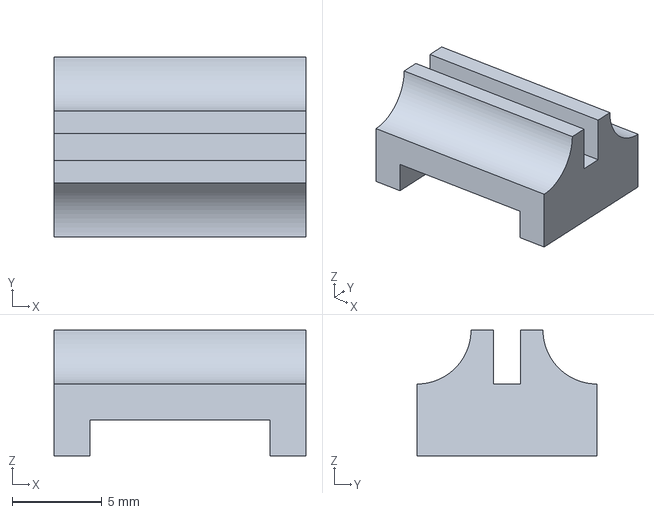
[picture p91: CAD file, 2022-03-30]
Hardware/3D files/Solární panely/Solární panel - Klip 1.3mf
14.0 x 10.0 x 7.00 mm
