Majklzbastlirny/WeatherStation/Hardware/3D files/Štít/Štít - Krytka.3mf

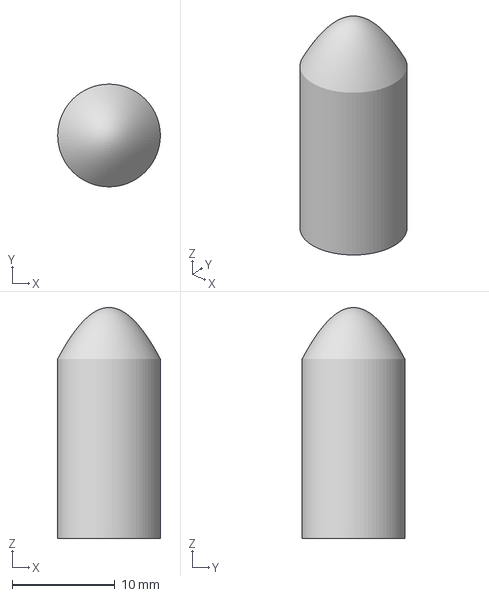
[picture p92: CAD file, 2022-03-30]
Hardware/3D files/Štít/Štít - Krytka.3mf
10.00 x 10.00 x 22.5 mm
