Majklzbastlirny/WeatherStation/Hardware/3D files/Anemometr/Anemometr - Tělo.3mf

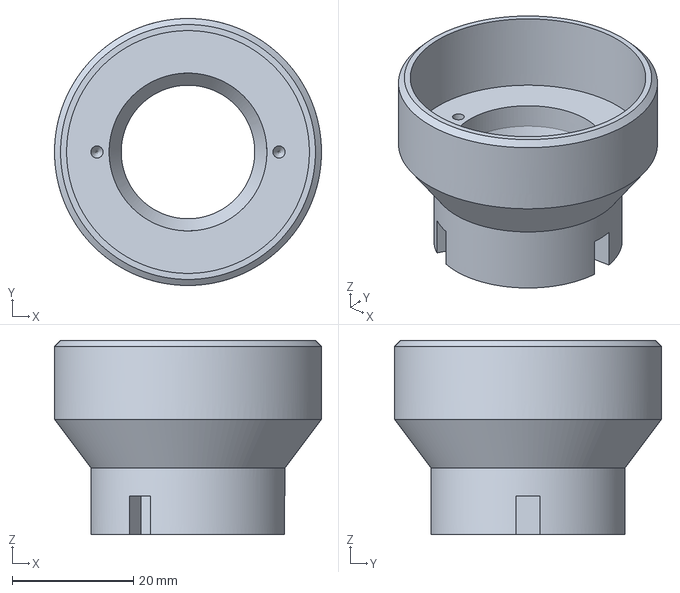
[picture p93: CAD file, 2022-03-30]
Hardware/3D files/Anemometr/Anemometr - Tělo.3mf
44.0 x 44.0 x 32.0 mm
