Majklzbastlirny/WeatherStation/Hardware/3D files/Držáky senzorů/Držáky senzorů - Štít.3mf

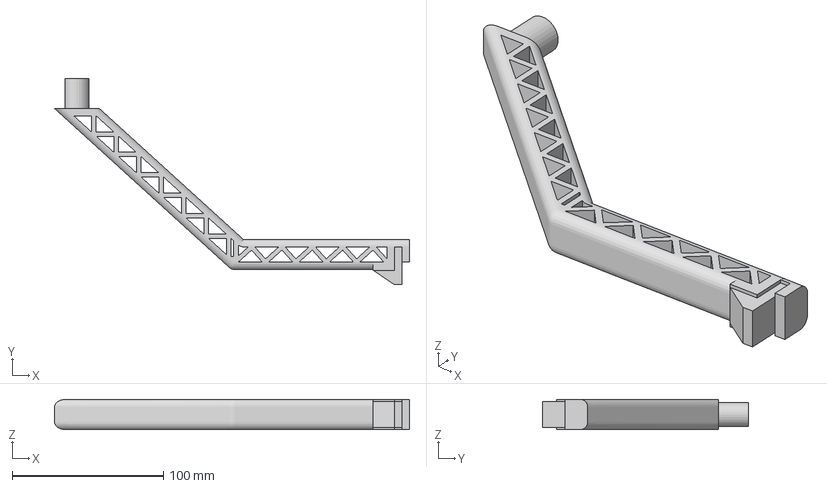
[picture p94: CAD file, 2022-03-30]
Hardware/3D files/Držáky senzorů/Držáky senzorů - Štít.3mf
235.0 x 136.6 x 20.0 mm
