Majklzbastlirny/WeatherStation/Hardware/3D files/Hlavní krabice/Hlavní krabice - Držák desky.3mf

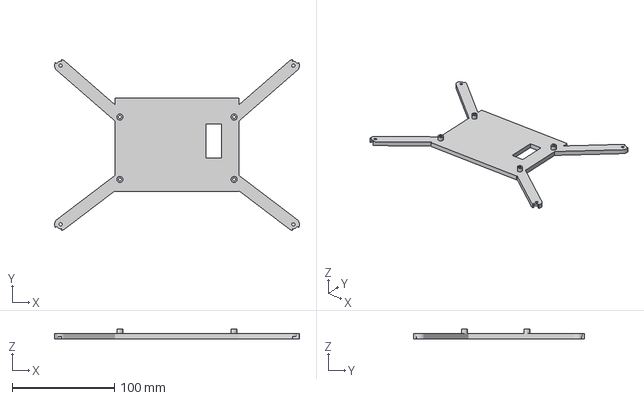
[picture p96: CAD file, 2022-03-30]
Hardware/3D files/Hlavní krabice/Hlavní krabice - Držák desky.3mf
239.6 x 167.1 x 9.50 mm
