Majklzbastlirny/WeatherStation/Hardware/3D files/Korouhev/Korouhev - Držák.3mf

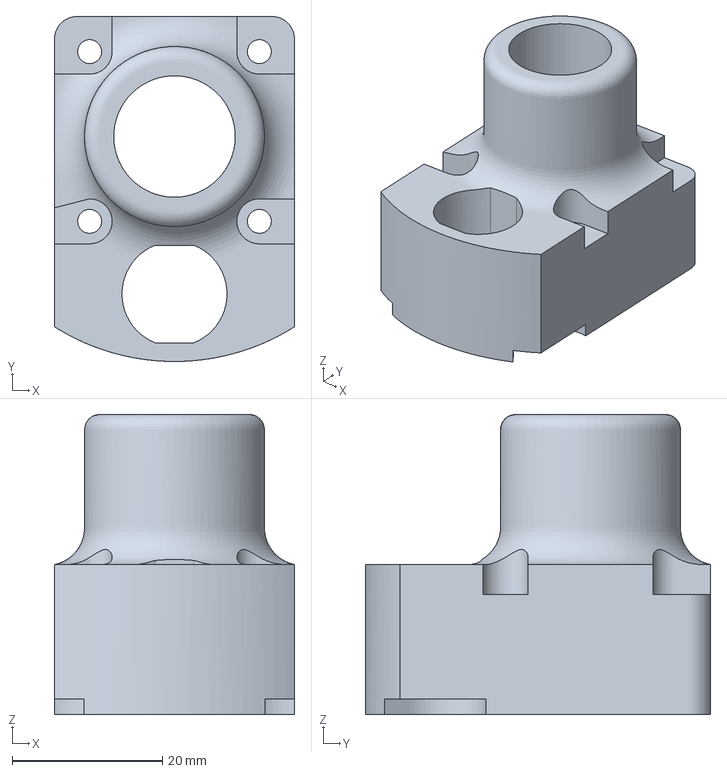
[picture p97: CAD file, 2022-03-30]
Hardware/3D files/Korouhev/Korouhev - Držák.3mf
32.0 x 46.0 x 40.0 mm
