Majklzbastlirny/WeatherStation/Hardware/3D files/OLED Zobrazovač/OLED Zobrazovač - Stojan.3mf

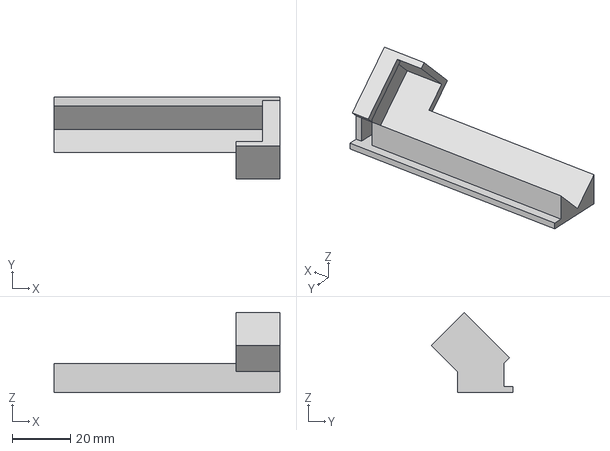
[picture p98: CAD file, 2022-03-30]
Hardware/3D files/OLED Zobrazovač/OLED Zobrazovač - Stojan.3mf
77.4 x 28.0 x 27.5 mm
