Majklzbastlirny/WeatherStation/Hardware/3D files/Solární panely/Solární panel - Klip 2.3mf

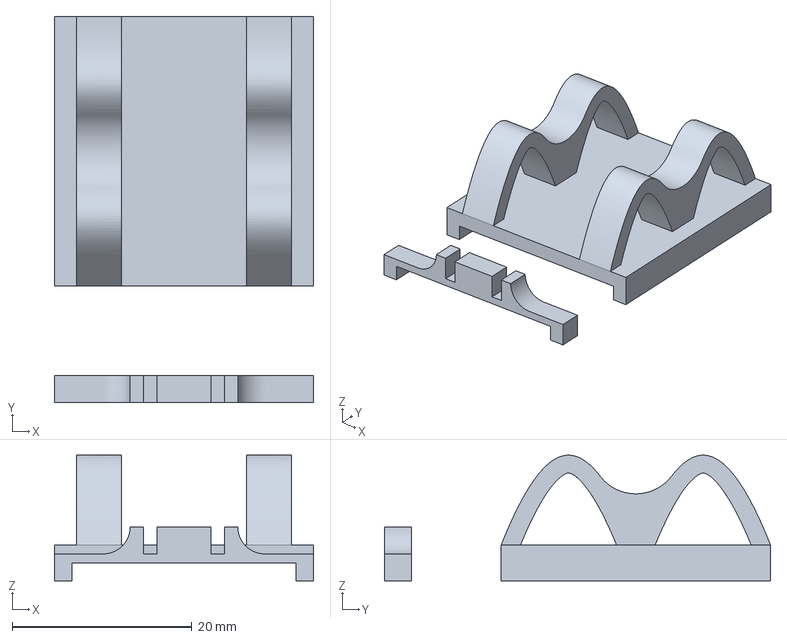
[picture p99: CAD file, 2022-03-30]
Hardware/3D files/Solární panely/Solární panel - Klip 2.3mf
28.9 x 43.0 x 14.0 mm
