Majklzbastlirny/WeatherStation/Hardware/3D files/Štít/Štít - Držák desky senzorů 1.3mf

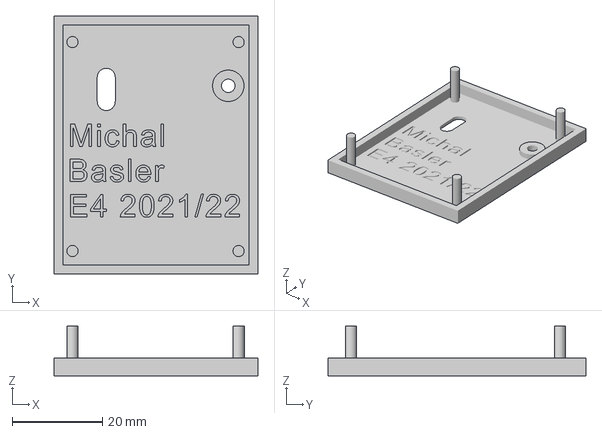
[picture p100: CAD file, 2022-03-30]
Hardware/3D files/Štít/Štít - Držák desky senzorů 1.3mf
45.3 x 57.3 x 11.0 mm
