Majklzbastlirny/WeatherStation/Hardware/3D files/Anemometr/Anemometr - Lopatka.3mf

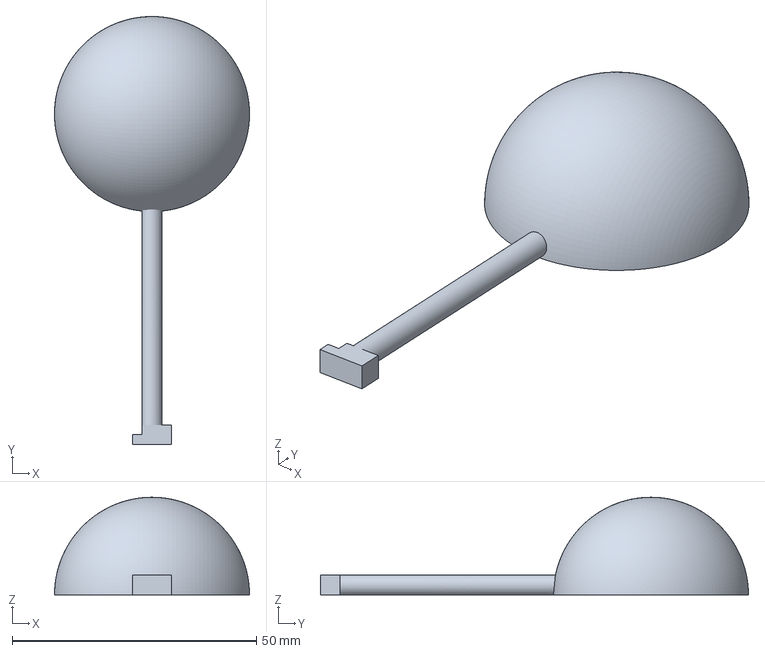
[picture p101: CAD file, 2022-03-30]
Hardware/3D files/Anemometr/Anemometr - Lopatka.3mf
39.9 x 87.5 x 19.9 mm
