Majklzbastlirny/WeatherStation/Hardware/3D files/Držáky senzorů/Držáky senzorů - Klip.3mf

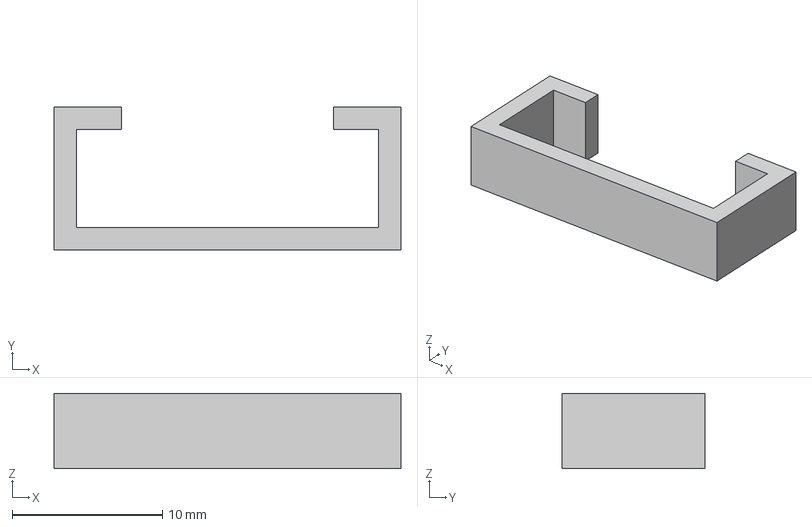
[picture p102: CAD file, 2022-03-30]
Hardware/3D files/Držáky senzorů/Držáky senzorů - Klip.3mf
23.1 x 9.50 x 5.00 mm
