Majklzbastlirny/WeatherStation/Hardware/3D files/E-Ink zobrazovač/E-Ink zobrazovač - Střed.3mf

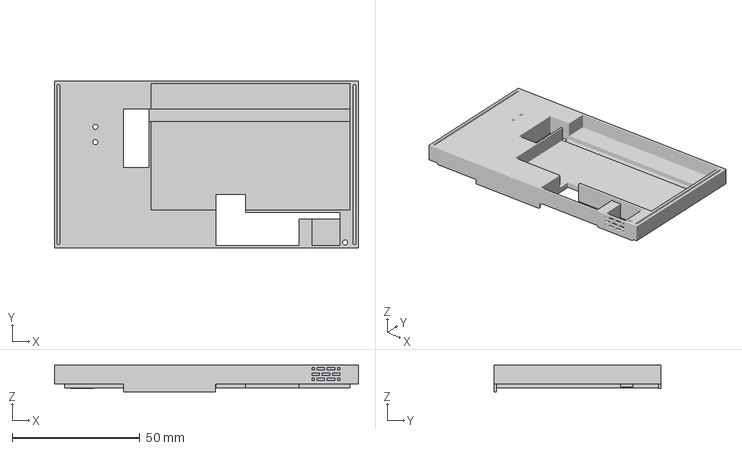
[picture p103: CAD file, 2022-03-30]
Hardware/3D files/E-Ink zobrazovač/E-Ink zobrazovač - Střed.3mf
119.0 x 65.5 x 10.5 mm
