Majklzbastlirny/WeatherStation/Hardware/3D files/Hlavní krabice/Hlavní krabice - Držák akumulátoru.3mf

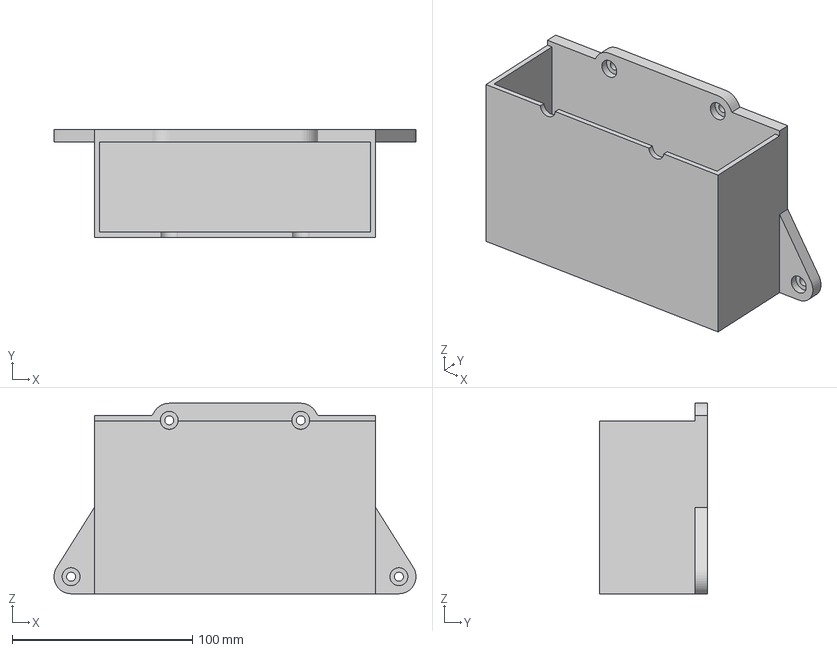
[picture p104: CAD file, 2022-03-30]
Hardware/3D files/Hlavní krabice/Hlavní krabice - Držák akumulátoru.3mf
201.0 x 60.0 x 105.8 mm
