Majklzbastlirny/WeatherStation/Hardware/3D files/Korouhev/Korouhev - Spodek těla.3mf

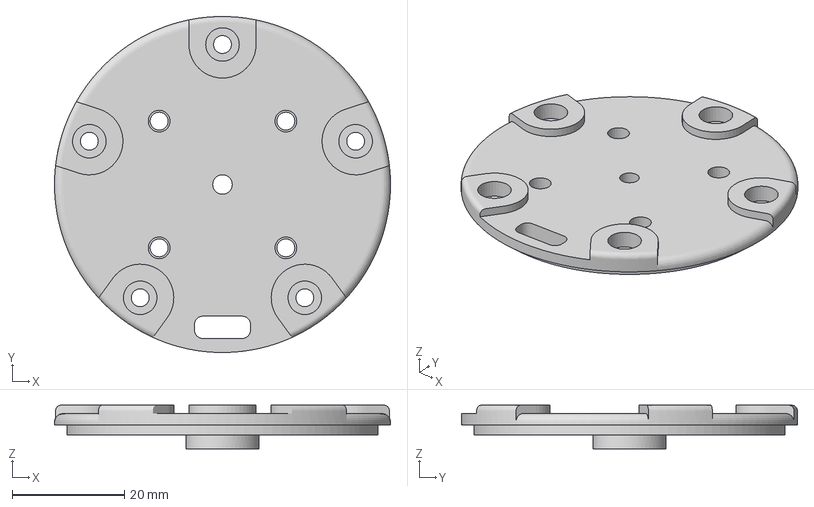
[picture p105: CAD file, 2022-03-30]
Hardware/3D files/Korouhev/Korouhev - Spodek těla.3mf
60.0 x 60.0 x 7.80 mm
