Majklzbastlirny/WeatherStation/Hardware/3D files/Solární panely/Solární panel - Držák všeho 1.3mf

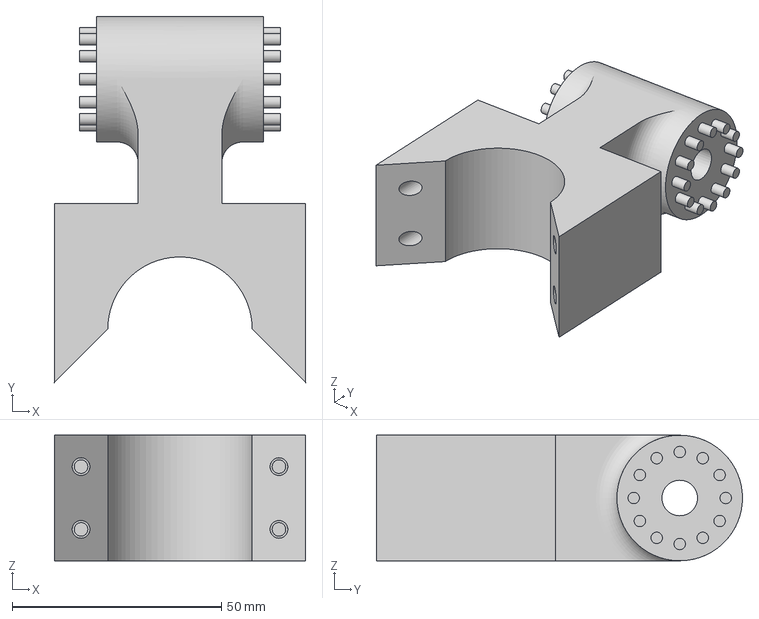
[picture p106: CAD file, 2022-03-30]
Hardware/3D files/Solární panely/Solární panel - Držák všeho 1.3mf
60.0 x 87.5 x 30.0 mm
