Majklzbastlirny/WeatherStation/Hardware/3D files/Štít/Štít - Vrch.3mf

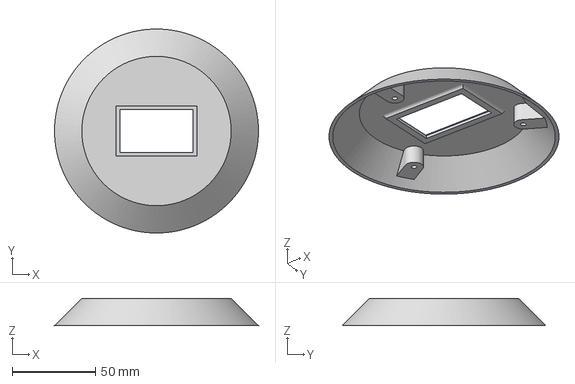
[picture p107: CAD file, 2022-03-30]
Hardware/3D files/Štít/Štít - Vrch.3mf
122.3 x 122.3 x 16.4 mm
