Majklzbastlirny/WeatherStation/Hardware/3D files/Korouhev/Korouhev - Vrch korouhve.3mf

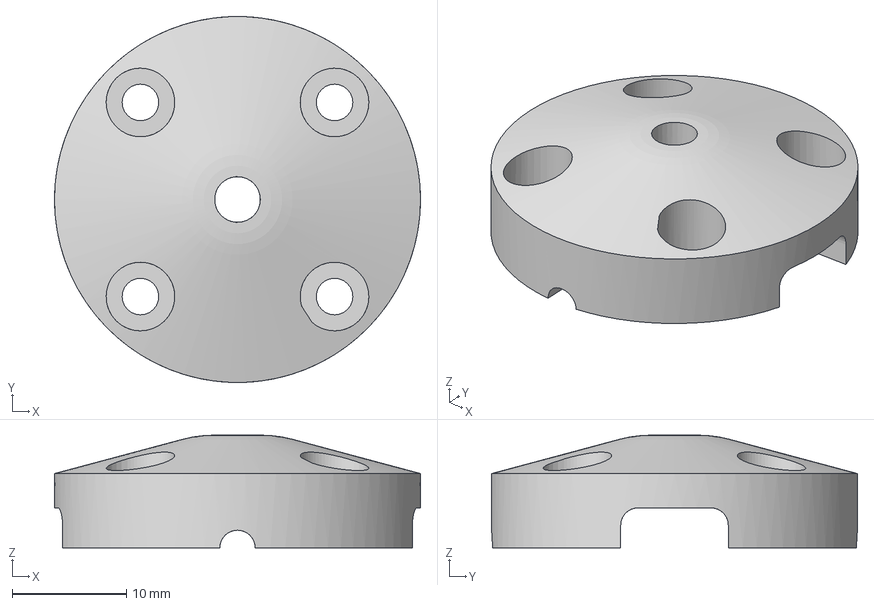
[picture p108: CAD file, 2022-03-30]
Hardware/3D files/Korouhev/Korouhev - Vrch korouhve.3mf
32.0 x 32.0 x 9.87 mm
