Majklzbastlirny/WeatherStation/Hardware/3D files/Solární panely/Solární panel - Kryt šroubu a matky.3mf

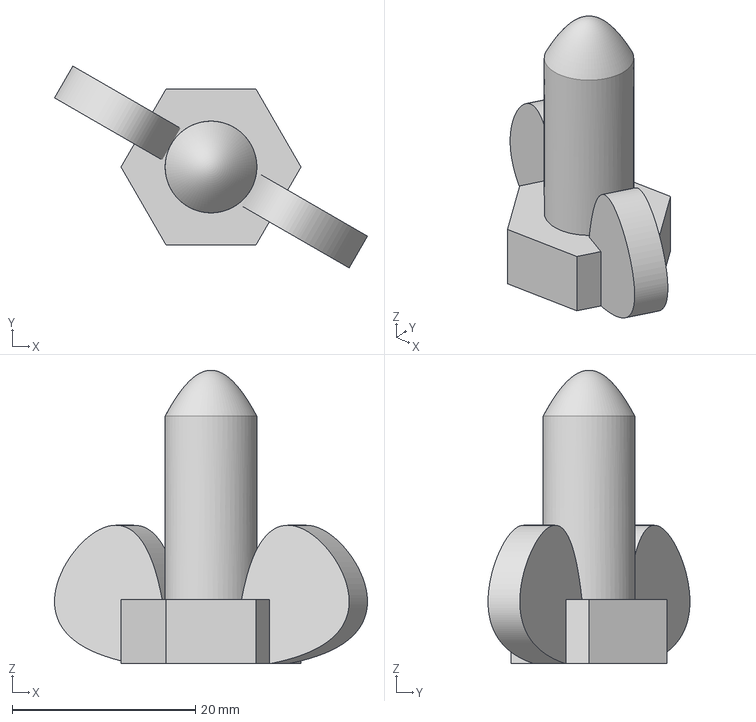
[picture p109: CAD file, 2022-03-30]
Hardware/3D files/Solární panely/Solární panel - Kryt šroubu a matky.3mf
34.1 x 22.0 x 32.0 mm
