Majklzbastlirny/WeatherStation/Hardware/3D files/Štít/Štít - Držák.3mf

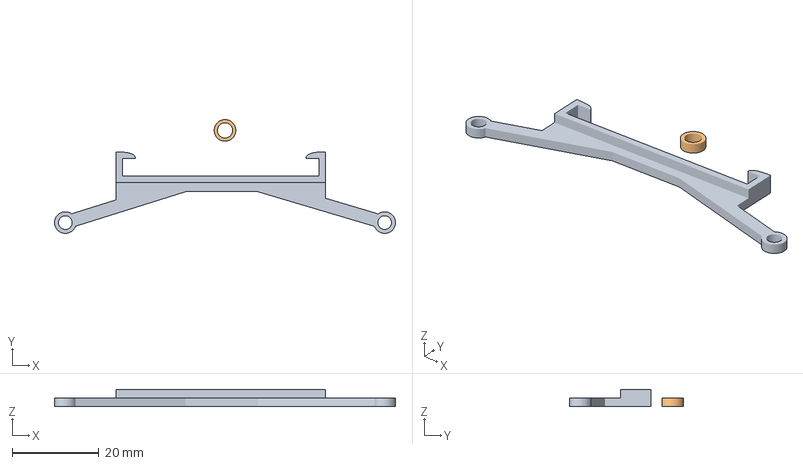
[picture p110: CAD file, 2022-03-30]
Hardware/3D files/Štít/Štít - Držák.3mf
78.6 x 26.2 x 4.00 mm
