Majklzbastlirny/WeatherStation/Hardware/3D files/Korouhev/Korouhev - Rotor.3mf

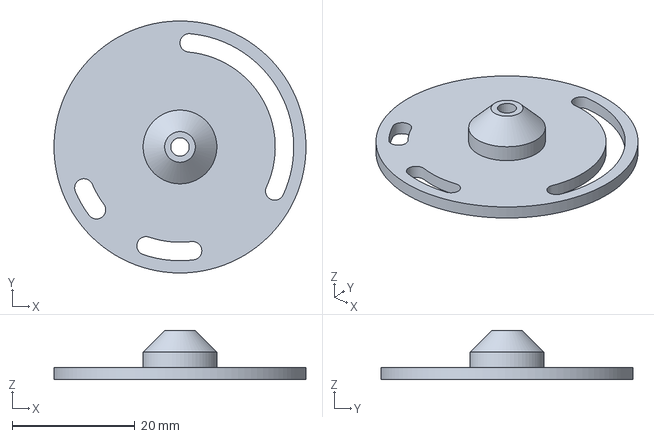
[picture p111: CAD file, 2022-03-30]
Hardware/3D files/Korouhev/Korouhev - Rotor.3mf
41.0 x 41.0 x 8.00 mm
