Majklzbastlirny/WeatherStation/Hardware/3D files/Solární panely/Solární panel - Držák všeho 2.3mf

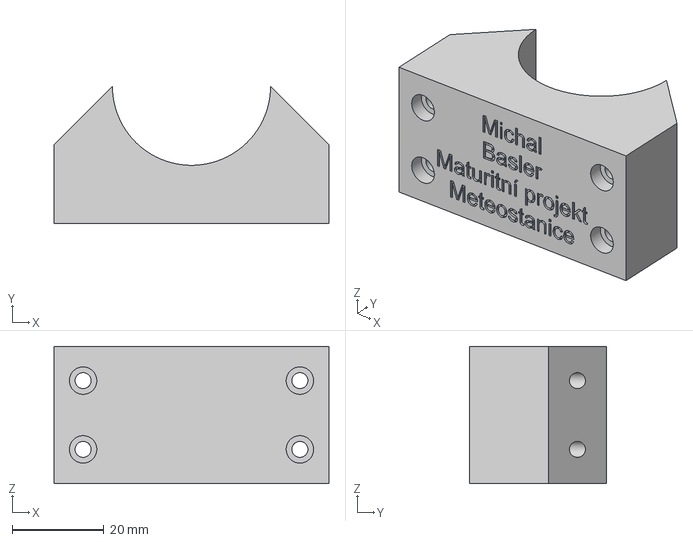
[picture p112: CAD file, 2022-03-30]
Hardware/3D files/Solární panely/Solární panel - Držák všeho 2.3mf
60.0 x 30.0 x 30.0 mm
