Majklzbastlirny/WeatherStation/Hardware/3D files/Štít/Štít - Střed.3mf

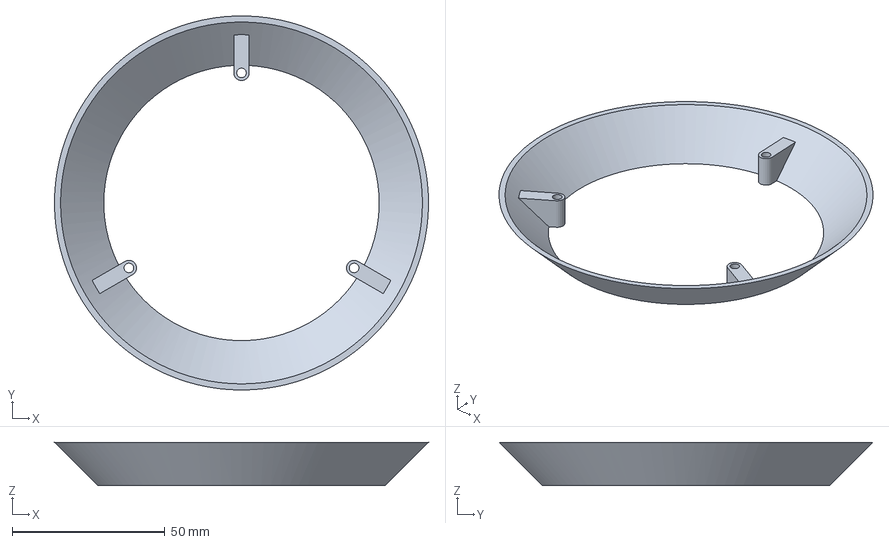
[picture p113: CAD file, 2022-03-30]
Hardware/3D files/Štít/Štít - Střed.3mf
122.3 x 122.3 x 14.1 mm
