Majklzbastlirny/WeatherStation/Hardware/3D files/Korouhev/Korouhev - Upínač nosu.3mf

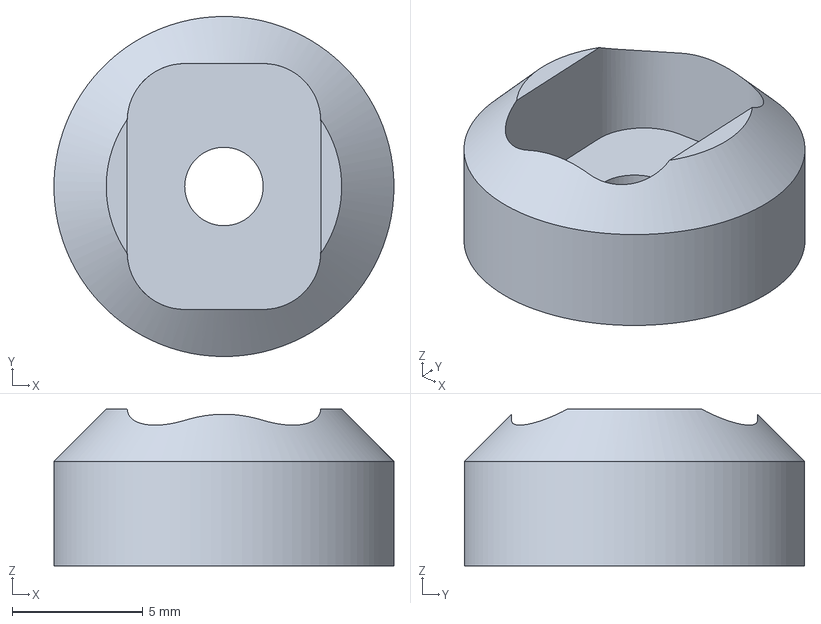
[picture p114: CAD file, 2022-03-30]
Hardware/3D files/Korouhev/Korouhev - Upínač nosu.3mf
13.0 x 13.0 x 6.00 mm
