Majklzbastlirny/WeatherStation/Hardware/3D files/Štít/Štít - Držák desky senzorů 2.3mf

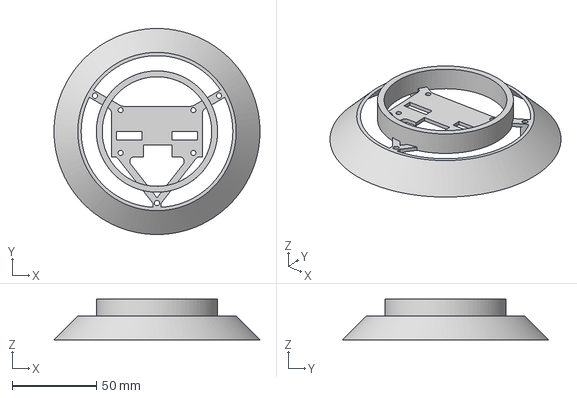
[picture p115: CAD file, 2022-03-30]
Hardware/3D files/Štít/Štít - Držák desky senzorů 2.3mf
122.3 x 122.3 x 24.0 mm
