Majklzbastlirny/WeatherStation/Hardware/3D files/Korouhev/Korouhev - Nos.3mf

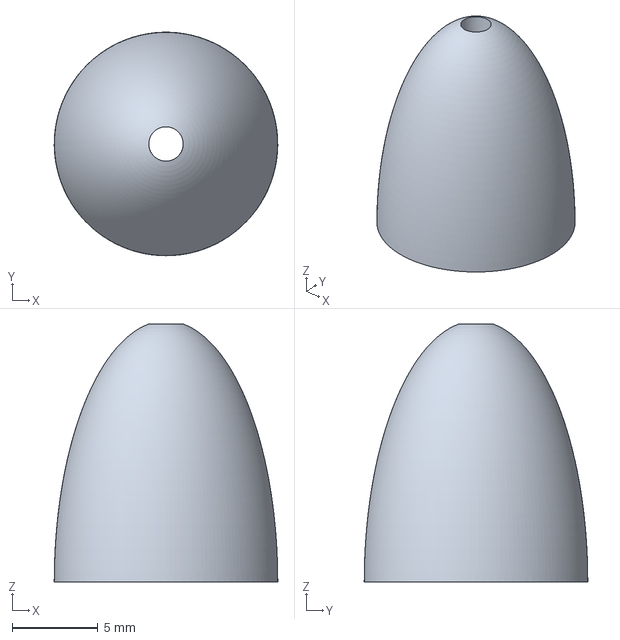
[picture p116: CAD file, 2022-03-30]
Hardware/3D files/Korouhev/Korouhev - Nos.3mf
13.0 x 13.0 x 15.0 mm
