Majklzbastlirny/WeatherStation/Hardware/3D files/Korouhev/Korouhev - Stabilizátor.3mf

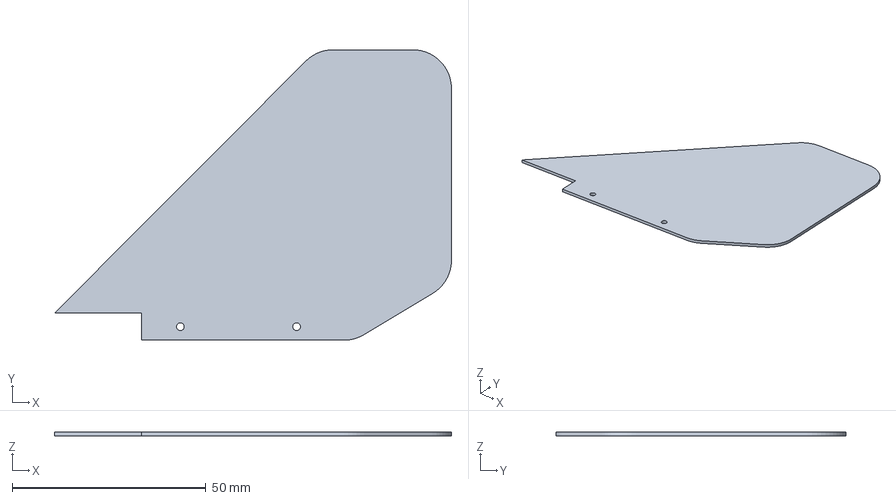
[picture p117: CAD file, 2022-03-30]
Hardware/3D files/Korouhev/Korouhev - Stabilizátor.3mf
102.5 x 75.0 x 1.00 mm
