Majklzbastlirny/WeatherStation/Hardware/3D files/Korouhev/Korouhev - Vrch těla.3mf

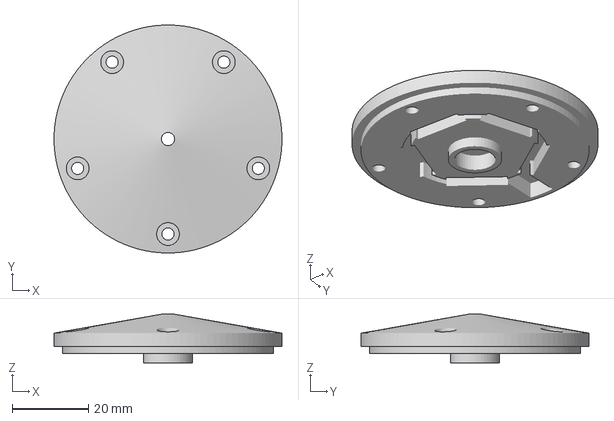
[picture p118: CAD file, 2022-03-30]
Hardware/3D files/Korouhev/Korouhev - Vrch těla.3mf
60.0 x 60.0 x 12.8 mm
