Majklzbastlirny/WeatherStation/Hardware/3D files/Korouhev/Korouhev - Držák LED.3mf

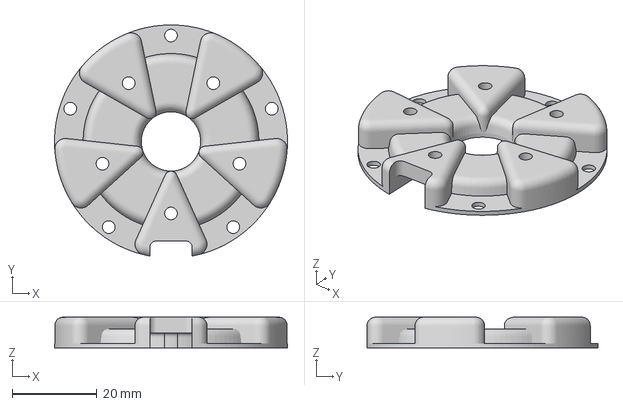
[picture p119: CAD file, 2022-03-30]
Hardware/3D files/Korouhev/Korouhev - Držák LED.3mf
55.0 x 54.5 x 7.25 mm
