Majklzbastlirny/WeatherStation/Hardware/3D files/Korouhev/Korouhev - Spodek korouhve.3mf

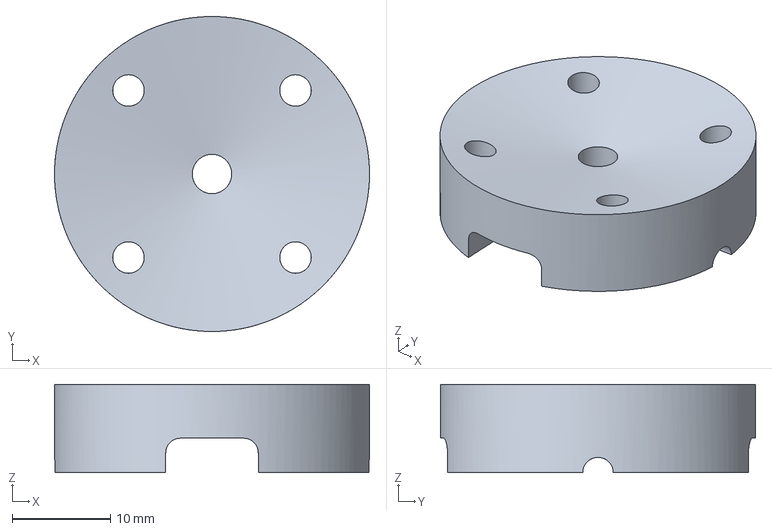
[picture p120: CAD file, 2022-03-30]
Hardware/3D files/Korouhev/Korouhev - Spodek korouhve.3mf
32.0 x 32.0 x 8.97 mm
