Majklzbastlirny/WeatherStation/Documentation/Meteostanice - Vývojový diagram.pdf

## Vývojový diagram - Meteostanice

Meteostanice | Serverside

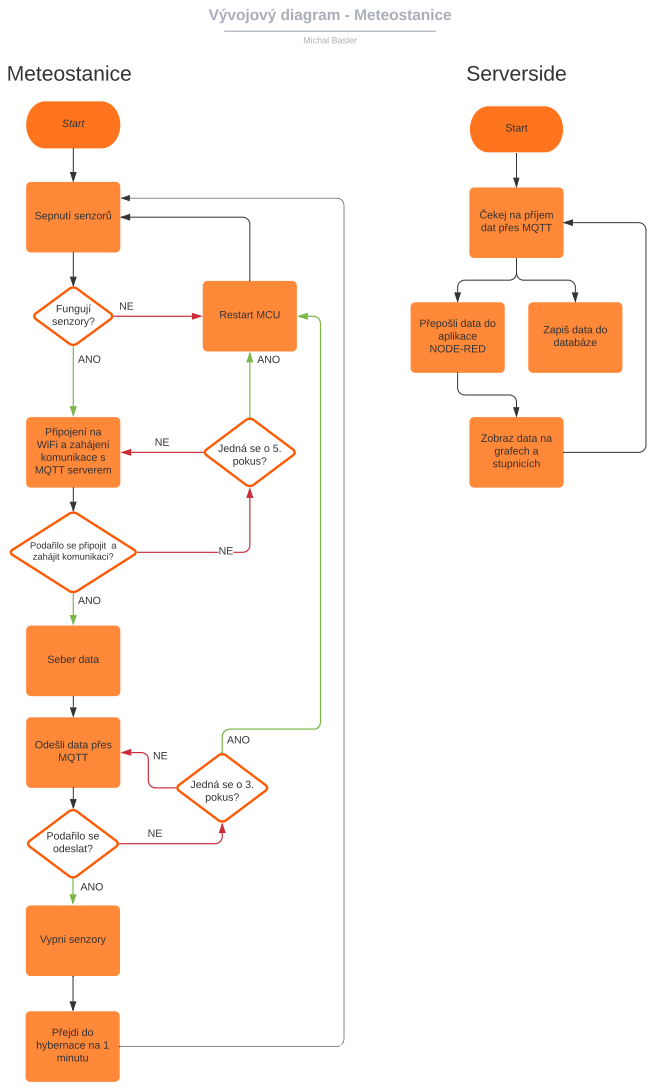
[picture p131: page 1]
Start; Fungují senzory?; Sepnutí senzor?; Michal Basler; Restart MCU; ANO; Jedná se o 5. pokus?; Seber data; Vypni senzory; Jedná se o 3. pokus?

? ekej na p?íjem
dat p?es MQTT

P?epo?li data do
aplikace NODE-RED

Zapi? data do
databáze

P?ipojení na WiFi a zahájení

Zobraz data na
grafech a
stupnicích

komunikace s MQTT serverem

Poda?ilo se p?ipojit a
zahájit komunikaci?

Ode?li data p?es MQTT

Poda?ilo se
odeslat?

P?ejdi do
hybernace na 1 minutu
