Majklzbastlirny/WeatherStation/Code/WeatherStation_Displays/WeatherStation_Home_Unit-E-INK/MAX2.h

const uint32_t MAX2_width = 350;
const uint32_t MAX2_height = 175;
const uint8_t MAX2_data[(350*175)/2] = {
0x66, 0x55, 0x66, 0x76, 0x66, 0x68, 0x46, 0x94, 0x67, 0x58, 0xA6, 0x68, 0x87, 0x46, 0x43, 0x84, 0x76, 0x57, 0x89, 0x76, 0x57, 0x78, 0x76, 0x67, 0x87, 0x98, 0x7A, 0x57, 0x85, 0x96, 0x77, 0x76, 0x57, 0x89, 0x87, 0x86, 0x88, 0x66, 0x88, 0x79, 0x87, 0x87, 0x67, 0x66, 0x78, 0x97, 0x77, 0x88, 0xA9, 0x57, 0xBA, 0x9A, 0x79, 0xA8, 0x9A, 0xB8, 0x9B, 0x98, 0xAA, 0xA9, 0x8A, 0x88, 0x77, 0x78, 0x68, 0x76, 0x76, 0x88, 0x87, 0x77, 0x88, 0x98, 0x87, 0x97, 0x78, 0x7A, 0x66, 0x75, 0x79, 0xDD, 0xCB, 0x79, 0x79, 0x78, 0x87, 0x88, 0x87, 0x88, 0x89, 0x89, 0x76, 0x89, 0x77, 0x66, 0x76, 0x68, 0x76, 0x86, 0x98, 0x88, 0x79, 0x88, 0xA8, 0x57, 0x76, 0x89, 0x78, 0x88, 0x99, 0x78, 0x78, 0xB7, 0x99, 0xA9, 0xCA, 0xDB, 0x8D, 0xAA, 0x88, 0x9A, 0xA9, 0xAA, 0x9A, 0x88, 0x99, 0xC9, 0xB9, 0xAA, 0x9A, 0x9A, 0xB8, 0xCB, 0xAB, 0xB9, 0xA8, 0xBA, 0xBB, 0xAB, 0xBB, 0xBB, 0xA9, 0x99, 0xAB, 0xBB, 0x99, 0x89, 0x89, 0x77, 0xAA, 0x9A, 0x97, 0x99, 0x99, 0xCA, 0x9B, 0xBB, 0x9B, 0xAA, 0xBC, 0xCC, 0xB9, 0x9A, 0x9C, 0xBB, 0xAA, 0x9C, 0xBC, 0xCC, 0xEB, 0xBC, 0xCC, 0x9C, 0xBC, 0x97, 0xAC, 
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
	};
