Majklzbastlirny/WeatherStation/Code/WeatherStation_Displays/WeatherStation_Home_Unit-E-INK/opensans24b.h

#pragma once
#include "epd_driver.h"
const uint8_t OpenSans24BBitmaps[33495] = {
    0x78, 0x9C, 0x03, 0x00, 0x00, 0x00, 0x00, 0x01, 0x78, 0x9C, 0xFB, 0xF0, 0xFF, 0xFF, 0xFF, 0xFC,
    0x0F, 0x40, 0x22, 0xFE, 0x01, 0x90, 0xF0, 0xBF, 0x00, 0x24, 0xEC, 0x41, 0x84, 0xFE, 0x01, 0x20,
    0x21, 0xBF, 0x01, 0x44, 0x2C, 0x00, 0x12, 0xFC, 0x13, 0x60, 0x04, 0x5F, 0x03, 0x90, 0xE0, 0x2D,
    0x00, 0x11, 0x09, 0x40, 0x82, 0x27, 0x00, 0x48, 0x70, 0x3B, 0x00, 0x09, 0x2E, 0x10, 0xC1, 0x69,
    0x00, 0x22, 0x14, 0x80, 0x04, 0x87, 0x00, 0x90, 0x60, 0x67, 0x00, 0x12, 0x6C, 0x20, 0x82, 0x15,
    0x44, 0xB0, 0x30, 0xFC, 0x03, 0x11, 0x7F, 0xFF, 0xFF, 0x67, 0x66, 0x68, 0xEB, 0xE8, 0x60, 0x64,
    0x40, 0x03, 0x02, 0xCE, 0x4C, 0x0C, 0x0C, 0xBF, 0xFE, 0x9F, 0x67, 0x04, 0x59, 0xC4, 0x0B, 0x72,
    0x95, 0xFD, 0x47, 0x90, 0xFB, 0x40, 0x44, 0x3C, 0xD8, 0x55, 0x20, 0xDB, 0x38, 0x19, 0x8E, 0xFC,
    0xAF, 0x65, 0x00, 0x00, 0x88, 0x28, 0x72, 0xE4, 0x78, 0x9C, 0x15, 0xCA, 0xDB, 0x11, 0x43, 0x00,
    0x00, 0x44, 0xD1, 0x8D, 0x21, 0x8C, 0x67, 0x09, 0x4A, 0x50, 0x82, 0x52, 0xB4, 0xA0, 0x14, 0x25,
    0x28, 0x21, 0x25, 0xA4, 0x84, 0x94, 0xA0, 0x04, 0x31, 0x88, 0x89, 0x8F, 0x6B, 0xFD, 0xED, 0xEC,
    0xB9, 0x27, 0x54, 0xDA, 0xA1, 0xFB, 0xDF, 0x63, 0x83, 0xF6, 0x80, 0x42, 0x2B, 0x34, 0x3F, 0xC8,
    0xB5, 0x40, 0x6D, 0xCE, 0xF4, 0xB5, 0x9B, 0x53, 0xCD, 0x50, 0x9A, 0x93, 0x7B, 0x14, 0xE6, 0x58,
    0x93, 0x43, 0xF3, 0x53, 0x6F, 0x87, 0x7E, 0x23, 0xBD, 0x1C, 0x7A, 0x84, 0x1A, 0x1D, 0x7E, 0x20,
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
};
const UnicodeInterval OpenSans24BIntervals[] = {
    { 0x20, 0x7E, 0x0 },
    { 0xA0, 0xFF, 0x5F },
};
const GFXfont OpenSans24B = {
    (uint8_t*)OpenSans24BBitmaps,
    (GFXglyph*)OpenSans24BGlyphs,
    (UnicodeInterval*)OpenSans24BIntervals,
    2,
    1,
    68,
    54,
    -15,
};
